astoria-d/super-duper-nes/doc/us-keyboard.png

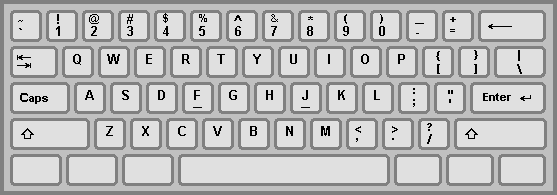
doc/us-keyboard.png
