astoria-d/super-duper-nes/doc/craft-work-diary/20161218/IMG_1332.JPG

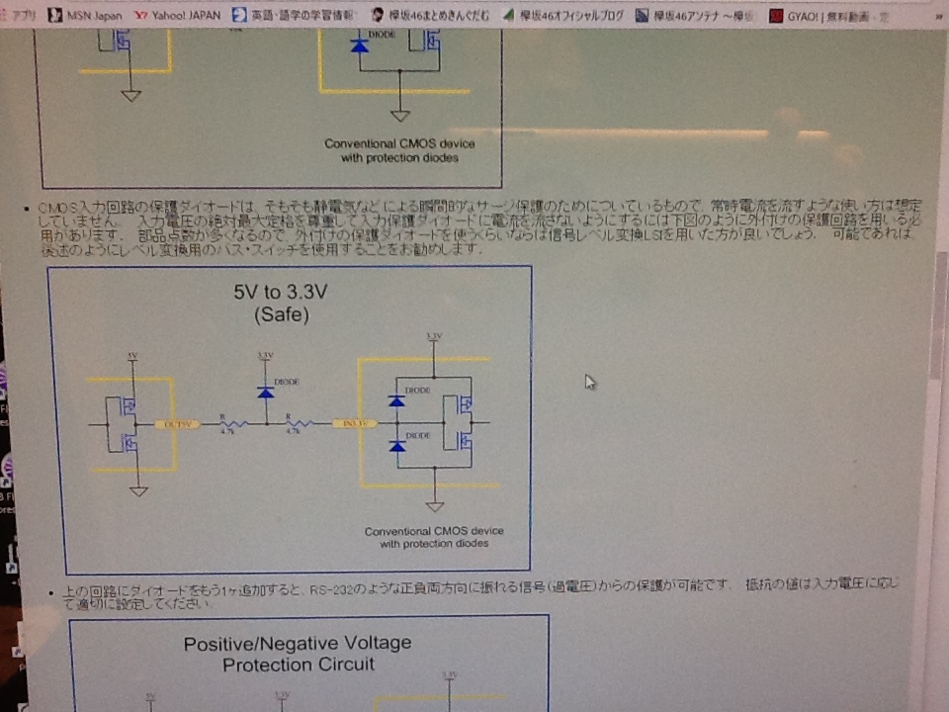
doc/craft-work-diary/20161218/IMG_1332.JPG
