astoria-d/super-duper-nes/doc/craft-work-diary/20161218/IMG_1335.JPG

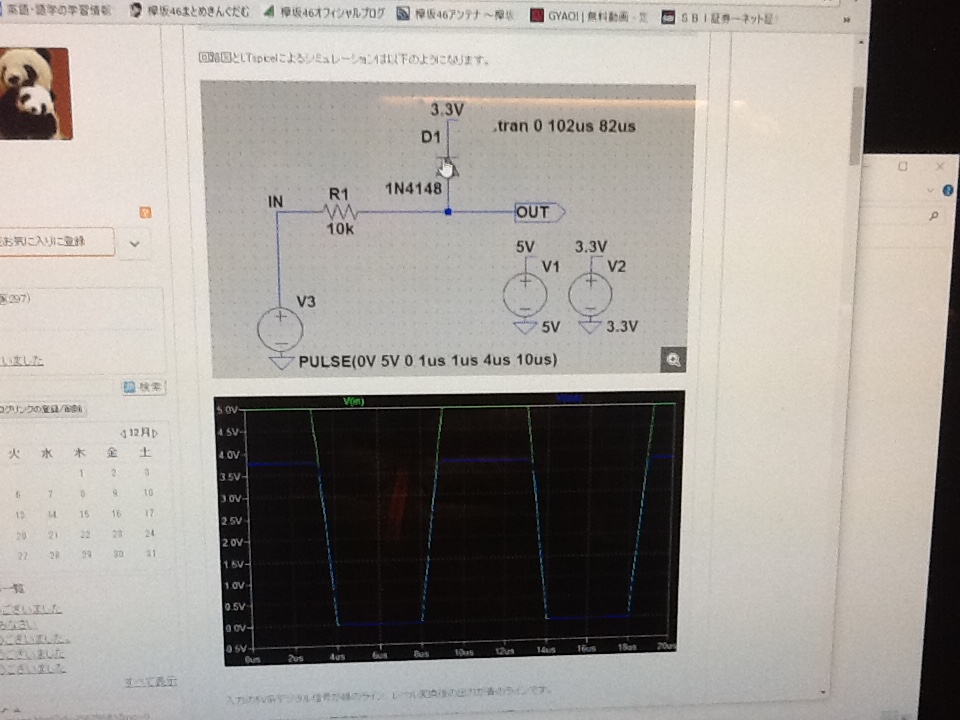
doc/craft-work-diary/20161218/IMG_1335.JPG
