astoria-d/super-duper-nes/doc/craft-work-diary/20161224/IMG_1348.JPG

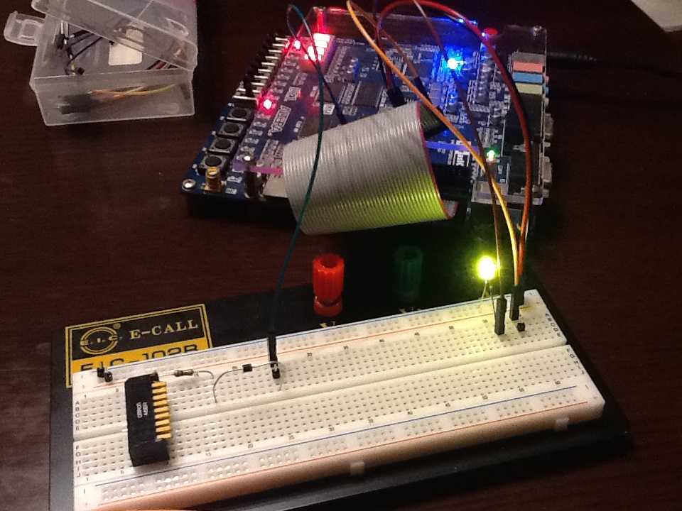
doc/craft-work-diary/20161224/IMG_1348.JPG
