astoria-d/super-duper-nes/doc/craft-work-diary/20161224/IMG_1349.JPG

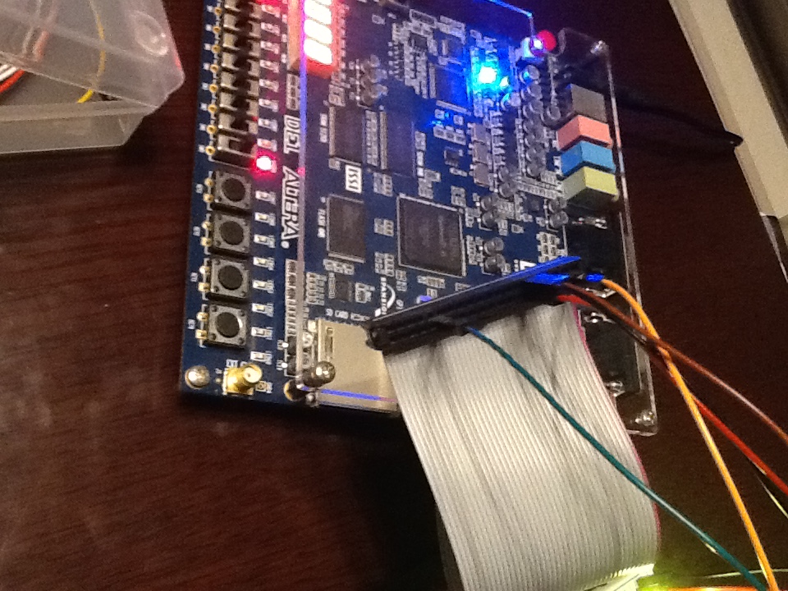
doc/craft-work-diary/20161224/IMG_1349.JPG
