astoria-d/super-duper-nes/doc/craft-work-diary/20161224/IMG_1350.JPG

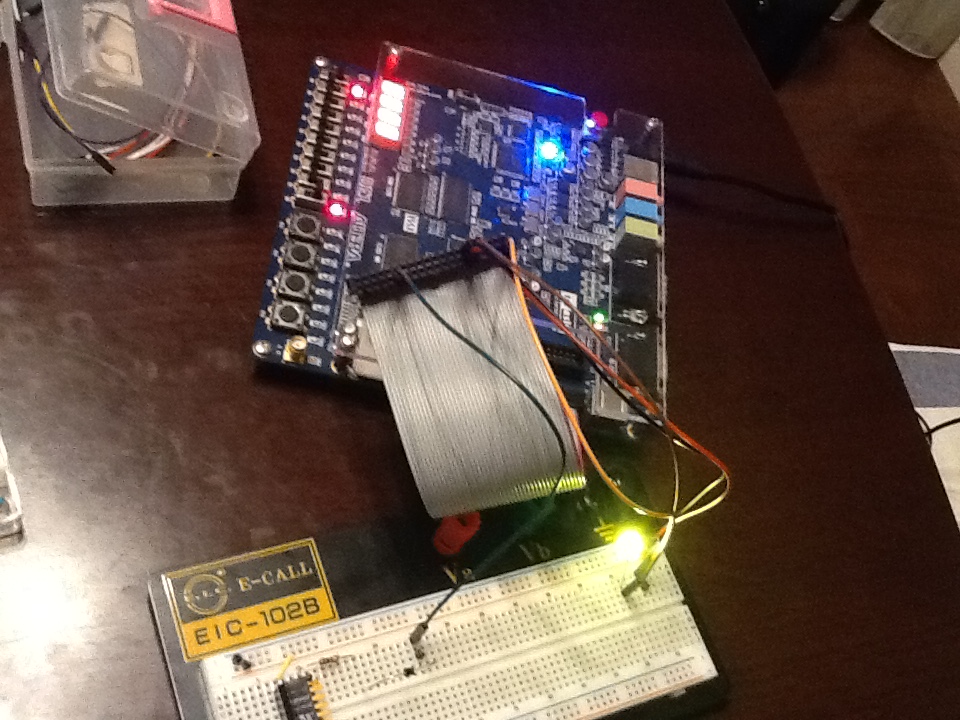
doc/craft-work-diary/20161224/IMG_1350.JPG
