astoria-d/super-duper-nes/doc/craft-work-diary/20161225/IMG_1356.JPG

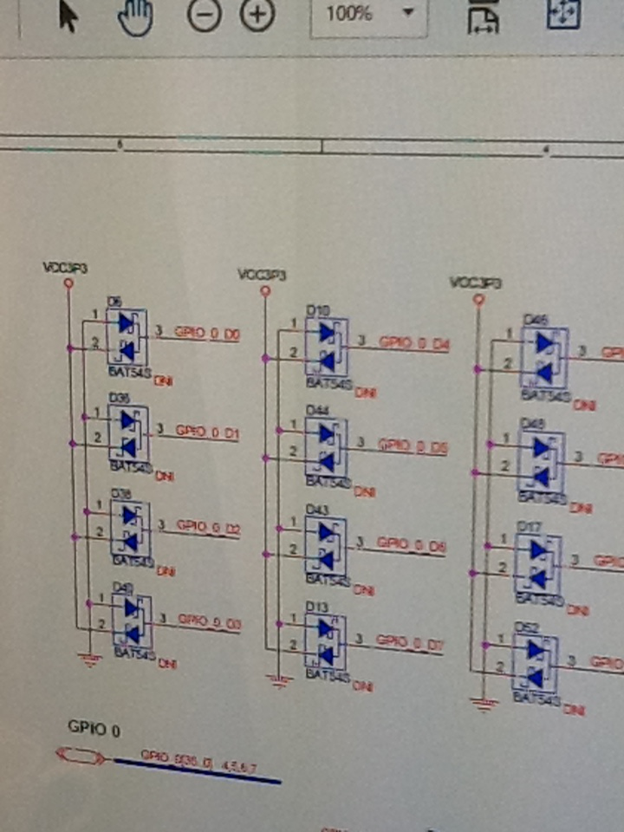
doc/craft-work-diary/20161225/IMG_1356.JPG
