astoria-d/super-duper-nes/doc/craft-work-diary/20161225/IMG_1360.JPG

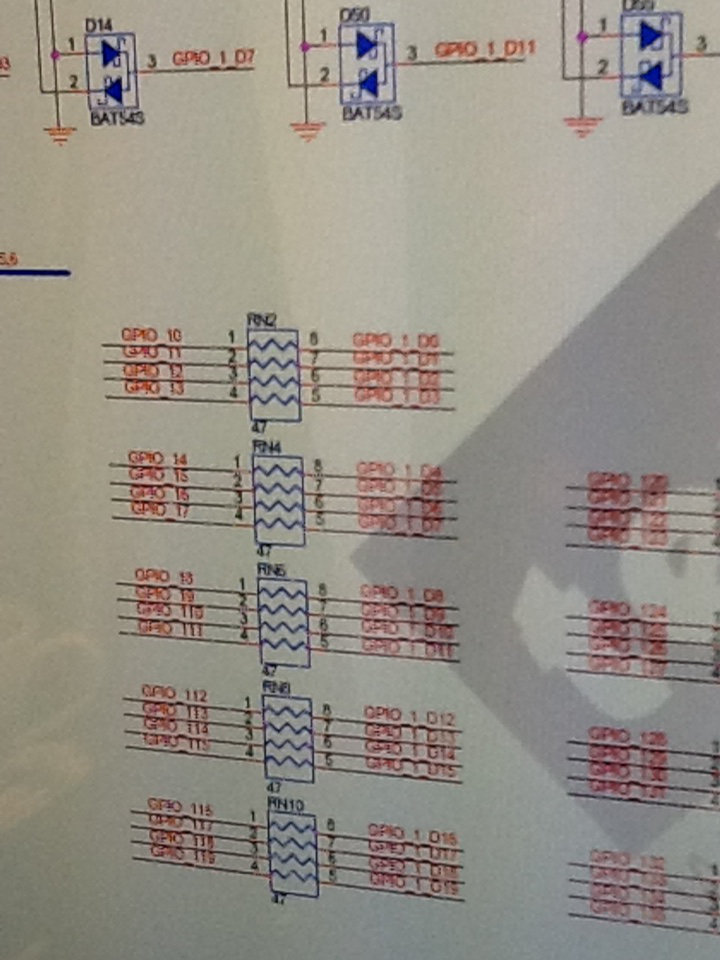
doc/craft-work-diary/20161225/IMG_1360.JPG
