astoria-d/super-duper-nes/doc/craft-work-diary/20161225/IMG_1362.JPG

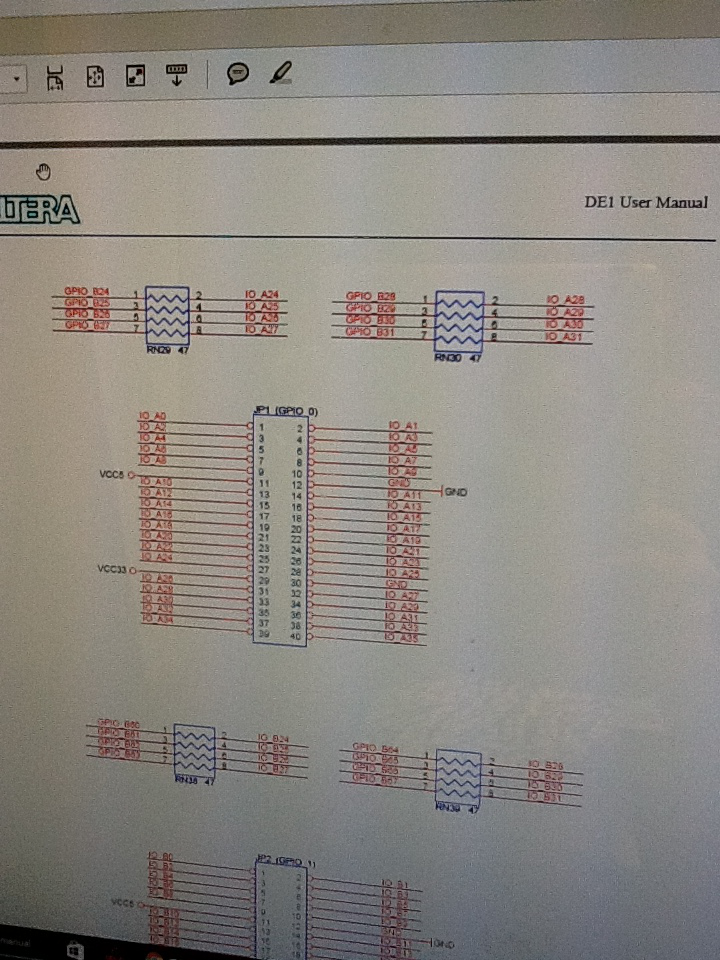
doc/craft-work-diary/20161225/IMG_1362.JPG
