astoria-d/super-duper-nes/doc/craft-work-diary/20170103/IMG_1378.JPG

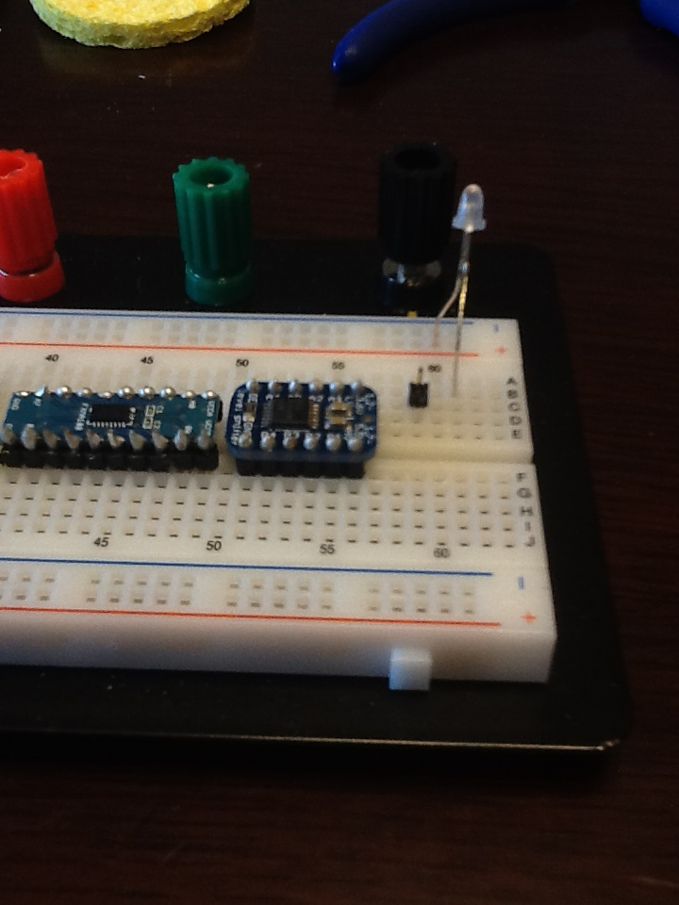
doc/craft-work-diary/20170103/IMG_1378.JPG
