astoria-d/super-duper-nes/doc/craft-work-diary/20170103/IMG_1380.JPG

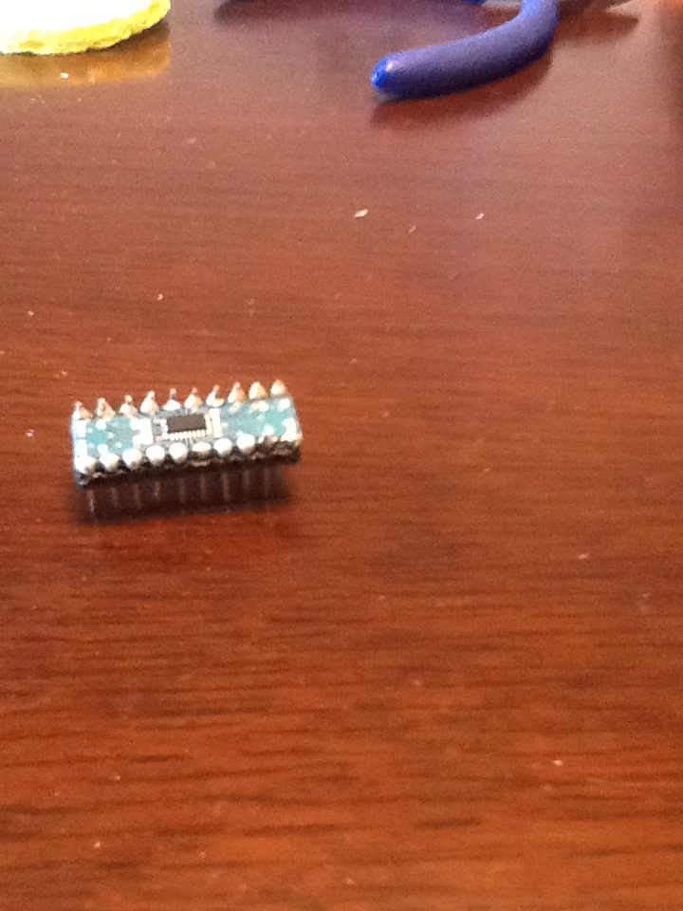
doc/craft-work-diary/20170103/IMG_1380.JPG
