astoria-d/super-duper-nes/doc/craft-work-diary/20170103/IMG_1381.JPG

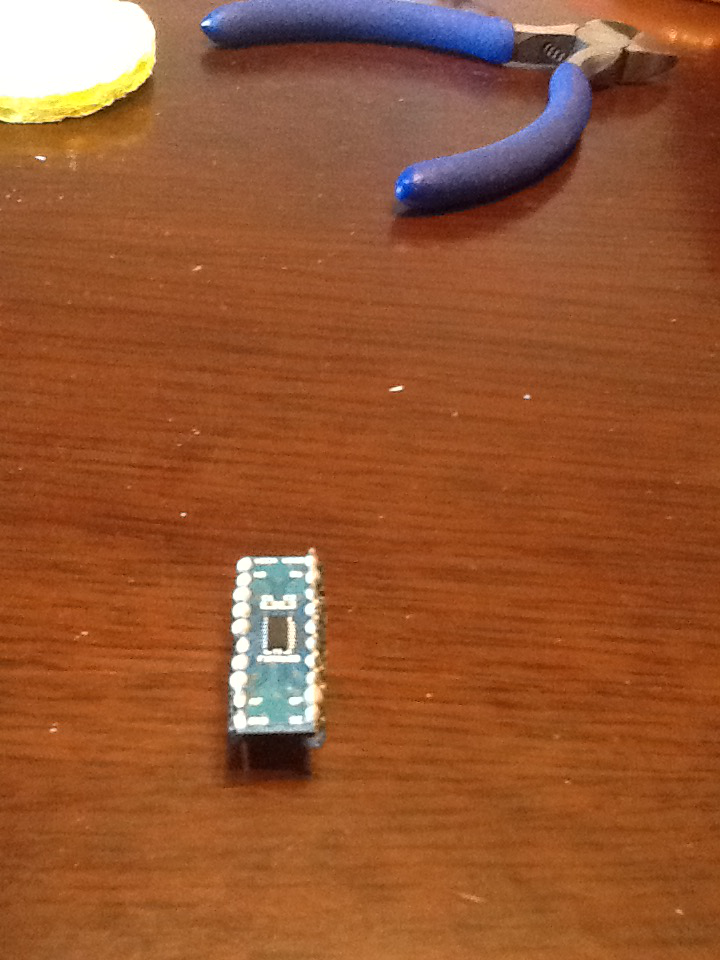
doc/craft-work-diary/20170103/IMG_1381.JPG
