astoria-d/super-duper-nes/doc/craft-work-diary/20170103/IMG_1382.JPG

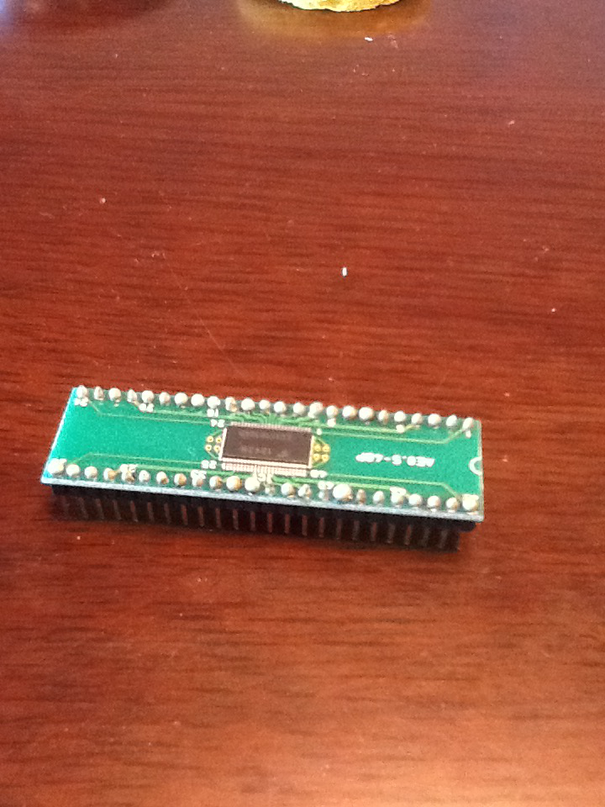
doc/craft-work-diary/20170103/IMG_1382.JPG
