astoria-d/super-duper-nes/doc/craft-work-diary/20170104/IMG_1393.JPG

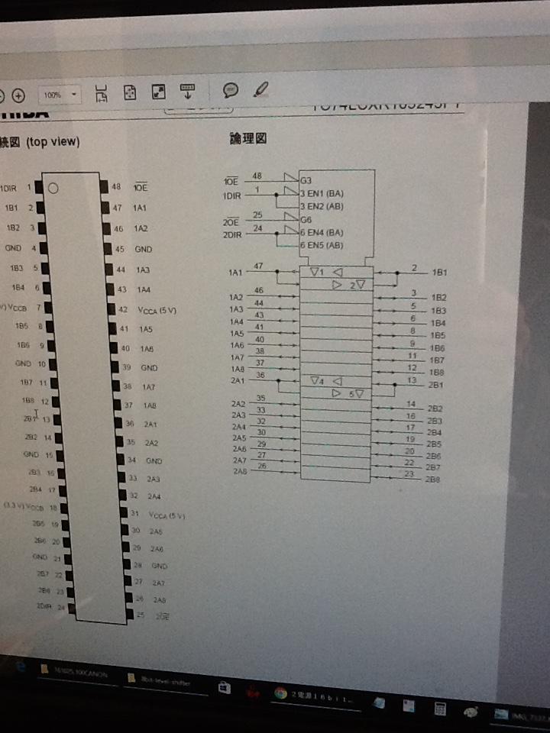
doc/craft-work-diary/20170104/IMG_1393.JPG
