astoria-d/super-duper-nes/doc/craft-work-diary/20170104/IMG_1396.JPG

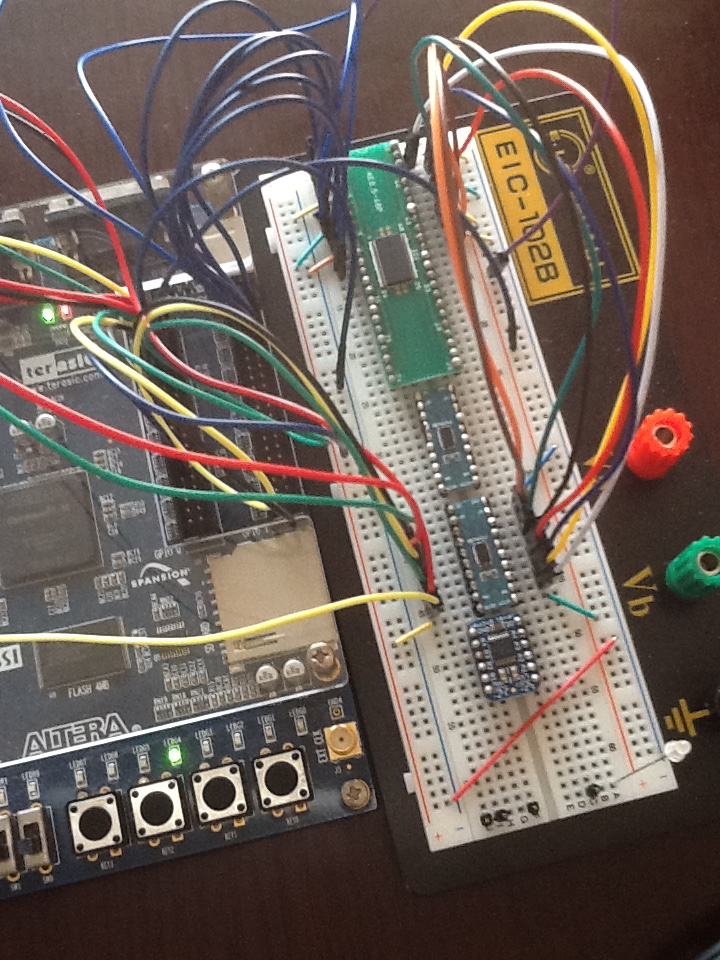
doc/craft-work-diary/20170104/IMG_1396.JPG
