astoria-d/super-duper-nes/doc/craft-work-diary/20170104/IMG_1401.JPG

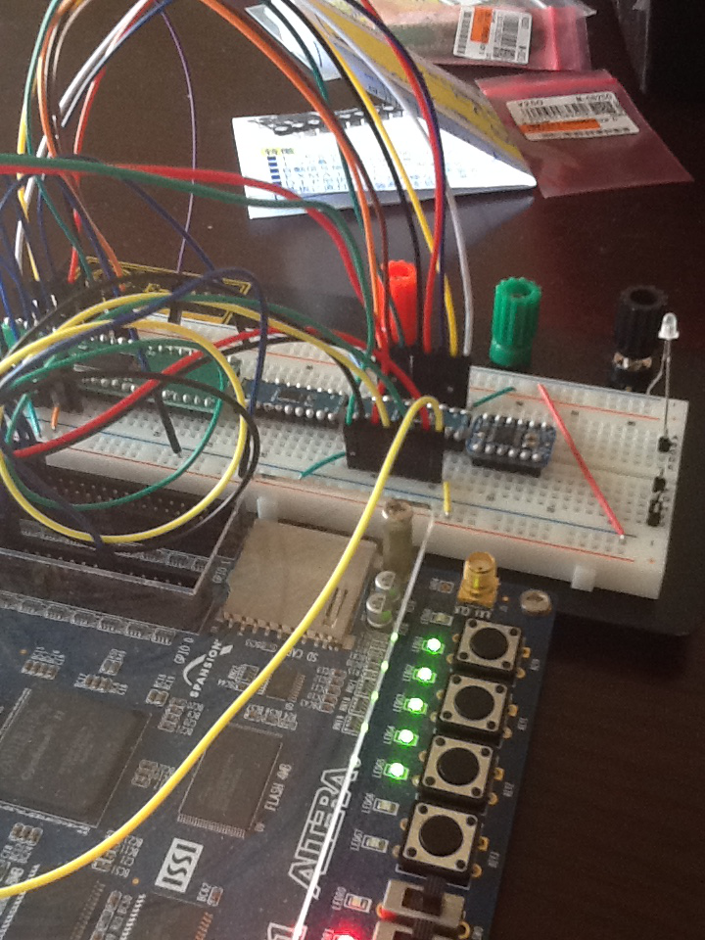
doc/craft-work-diary/20170104/IMG_1401.JPG
