astoria-d/super-duper-nes/doc/craft-work-diary/20170104/IMG_1402.JPG

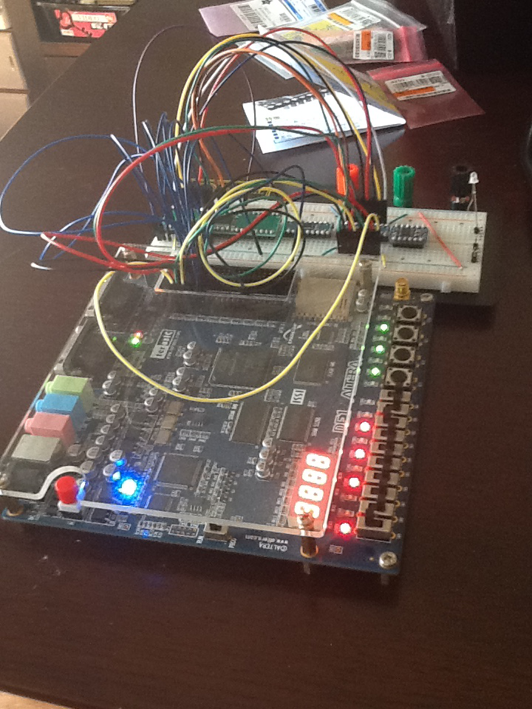
doc/craft-work-diary/20170104/IMG_1402.JPG
