astoria-d/super-duper-nes/doc/craft-work-diary/20170107/IMG_1409.JPG

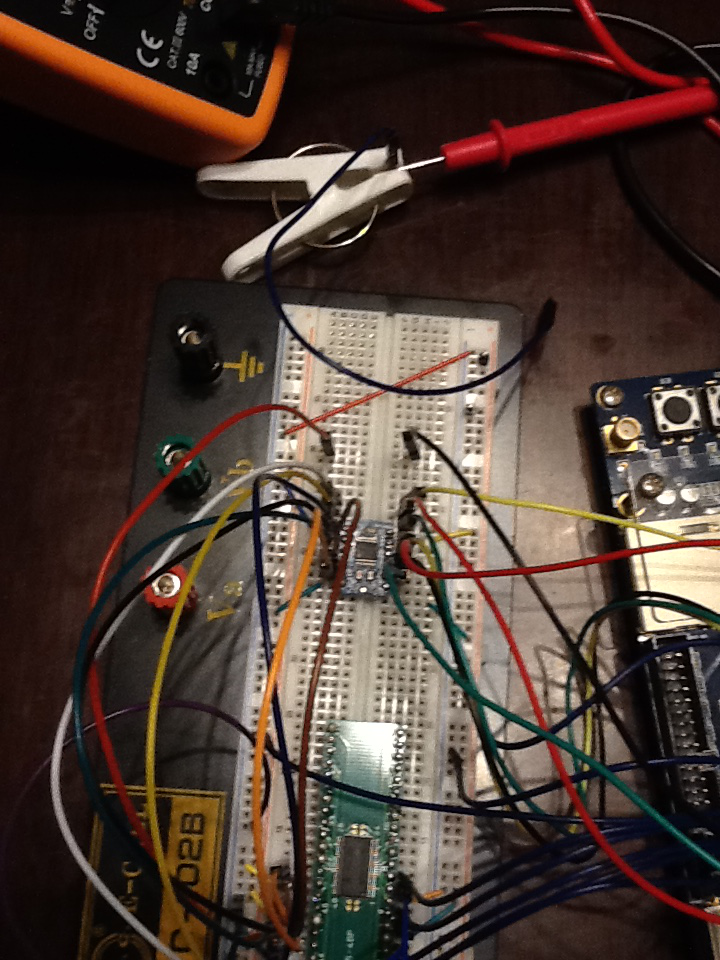
doc/craft-work-diary/20170107/IMG_1409.JPG
