astoria-d/super-duper-nes/doc/craft-work-diary/20170108/IMG_1414.JPG

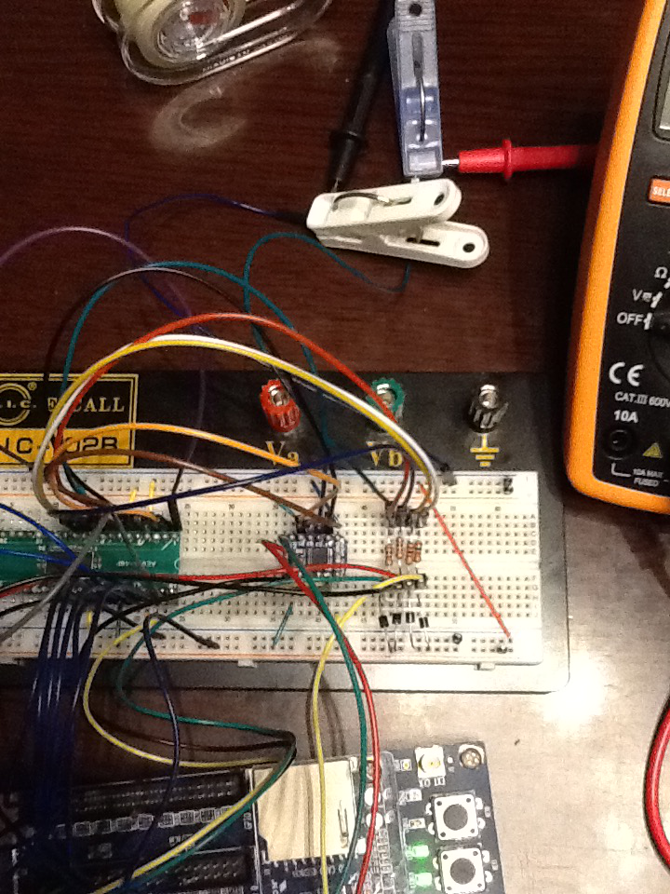
doc/craft-work-diary/20170108/IMG_1414.JPG
