astoria-d/super-duper-nes/doc/craft-work-diary/20170109/IMG_1426.PNG

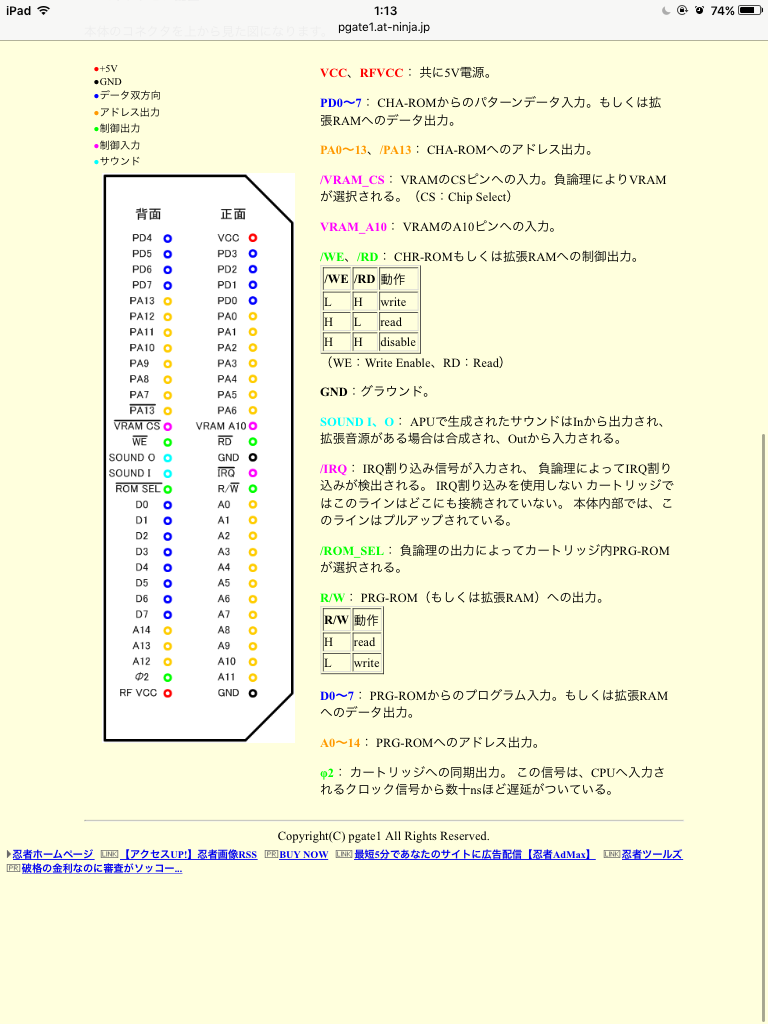
doc/craft-work-diary/20170109/IMG_1426.PNG
