astoria-d/super-duper-nes/doc/craft-work-diary/20170109/IMG_1438.JPG

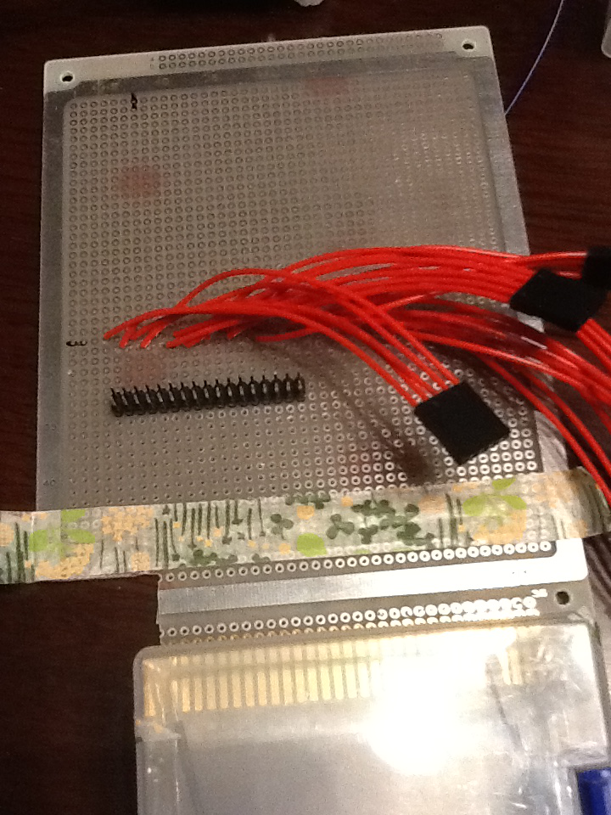
doc/craft-work-diary/20170109/IMG_1438.JPG
