astoria-d/super-duper-nes/doc/craft-work-diary/20170109/IMG_1439.JPG

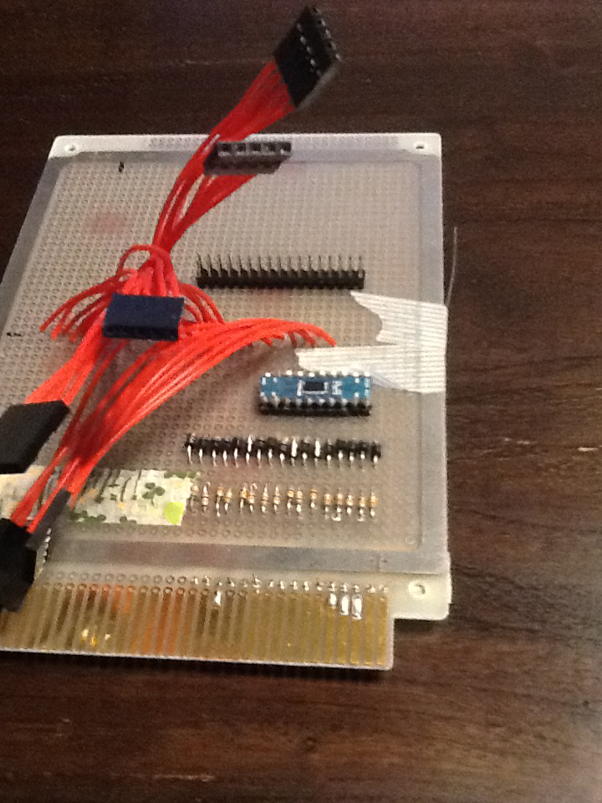
doc/craft-work-diary/20170109/IMG_1439.JPG
