astoria-d/super-duper-nes/doc/craft-work-diary/20170110/IMG_1443.JPG

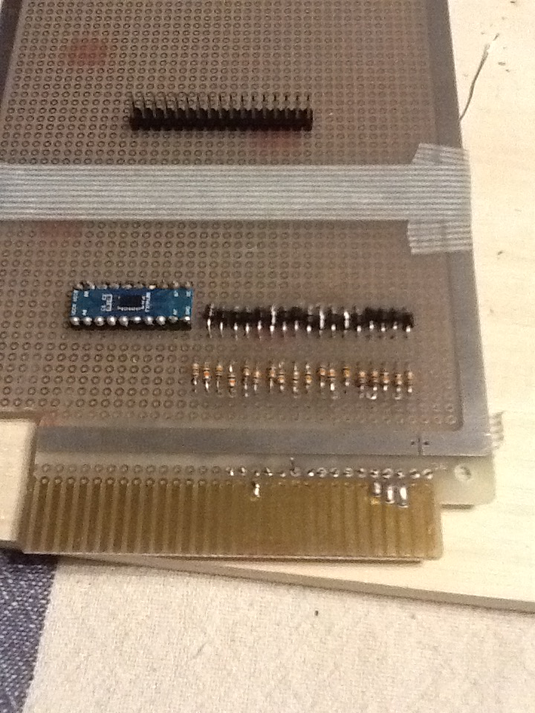
doc/craft-work-diary/20170110/IMG_1443.JPG
