astoria-d/super-duper-nes/doc/craft-work-diary/20170110/IMG_1444.JPG

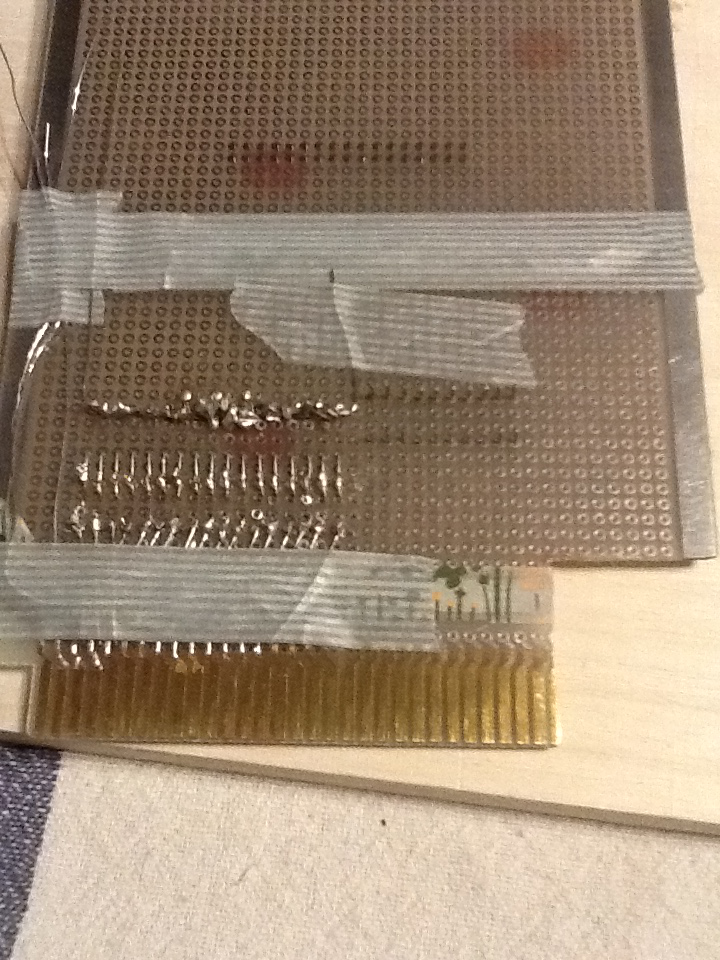
doc/craft-work-diary/20170110/IMG_1444.JPG
