astoria-d/super-duper-nes/doc/craft-work-diary/20170114/IMG_1446.JPG

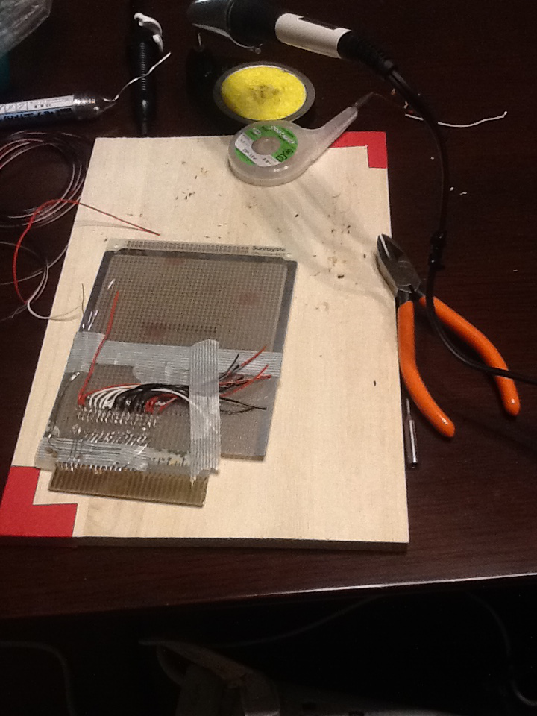
doc/craft-work-diary/20170114/IMG_1446.JPG
