astoria-d/super-duper-nes/doc/craft-work-diary/20170115/IMG_1449.JPG

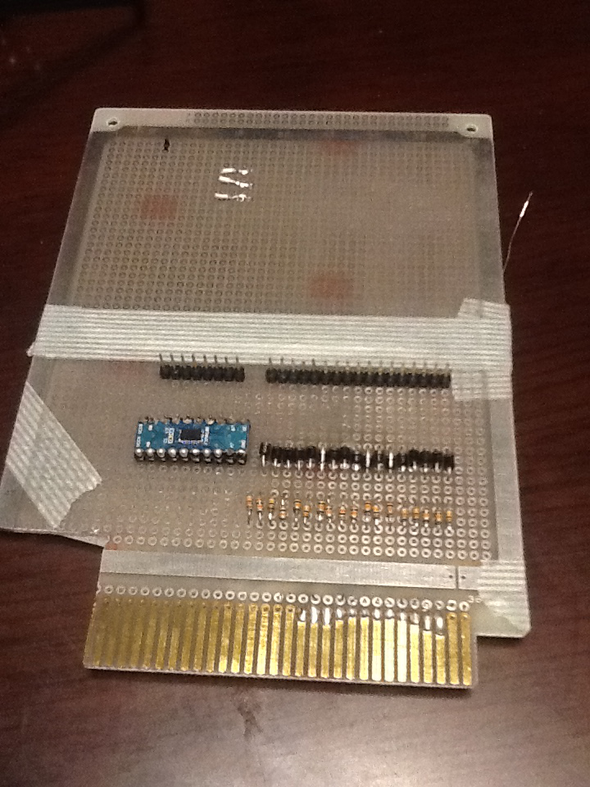
doc/craft-work-diary/20170115/IMG_1449.JPG
