astoria-d/super-duper-nes/doc/craft-work-diary/20170116/IMG_1457.JPG

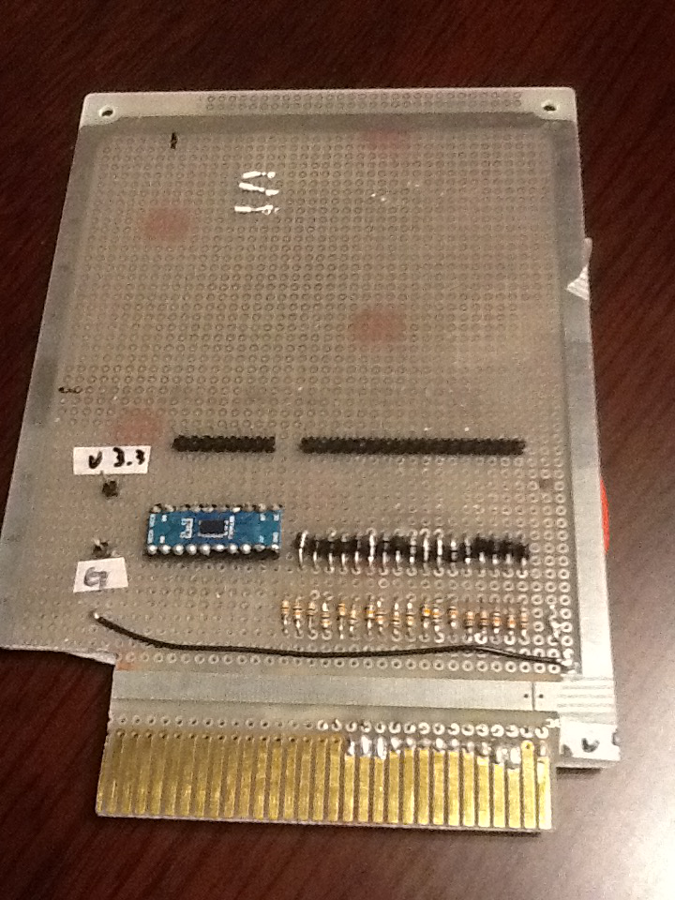
doc/craft-work-diary/20170116/IMG_1457.JPG
