astoria-d/super-duper-nes/doc/craft-work-diary/20170119/IMG_1460.JPG

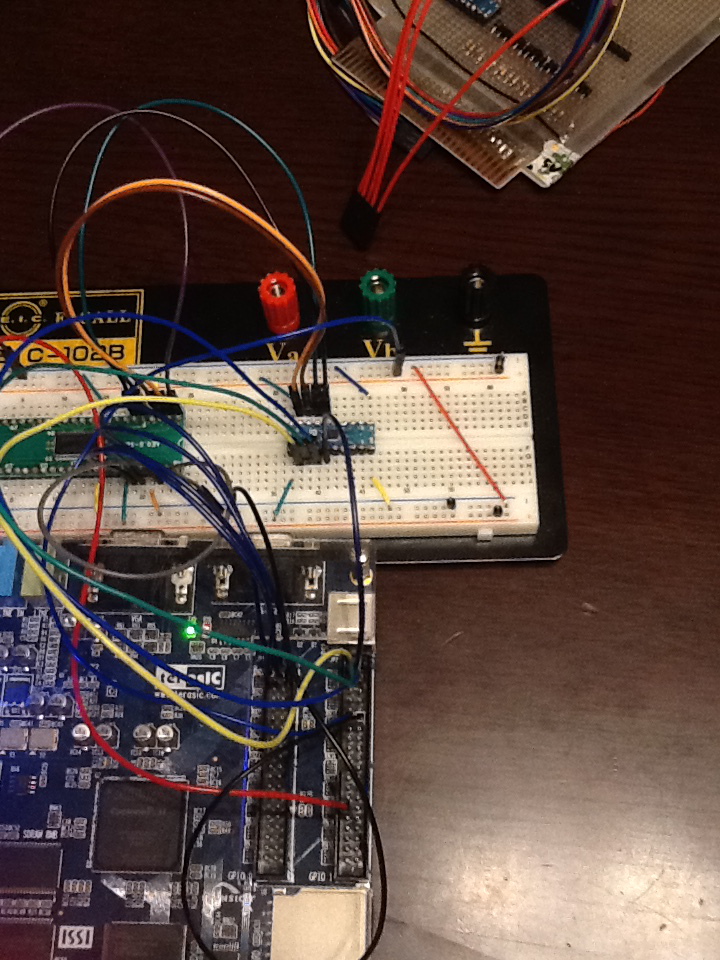
doc/craft-work-diary/20170119/IMG_1460.JPG
