astoria-d/super-duper-nes/doc/craft-work-diary/20170121/IMG_1466.JPG

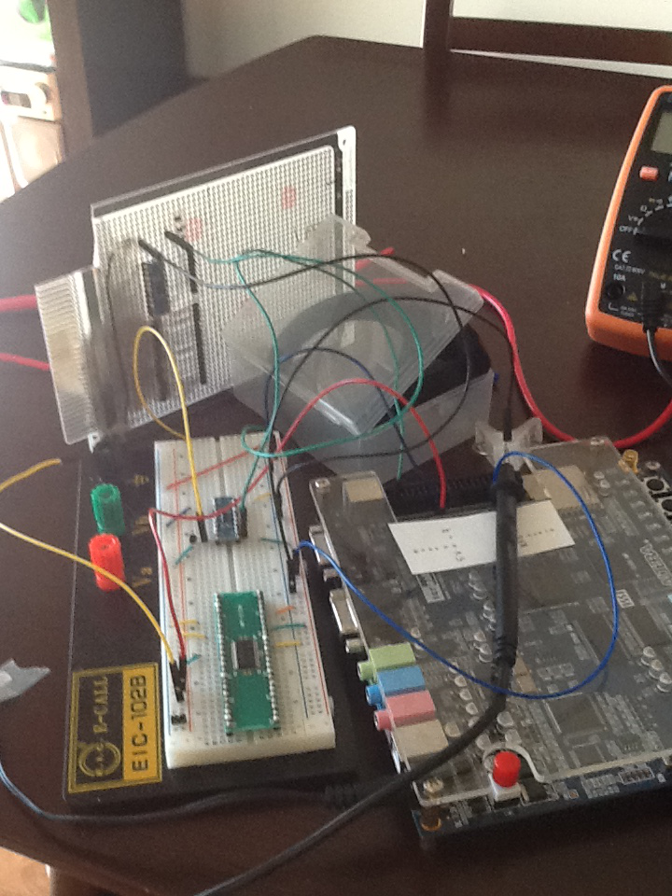
doc/craft-work-diary/20170121/IMG_1466.JPG
