astoria-d/super-duper-nes/doc/craft-work-diary/20170121/IMG_1471.JPG

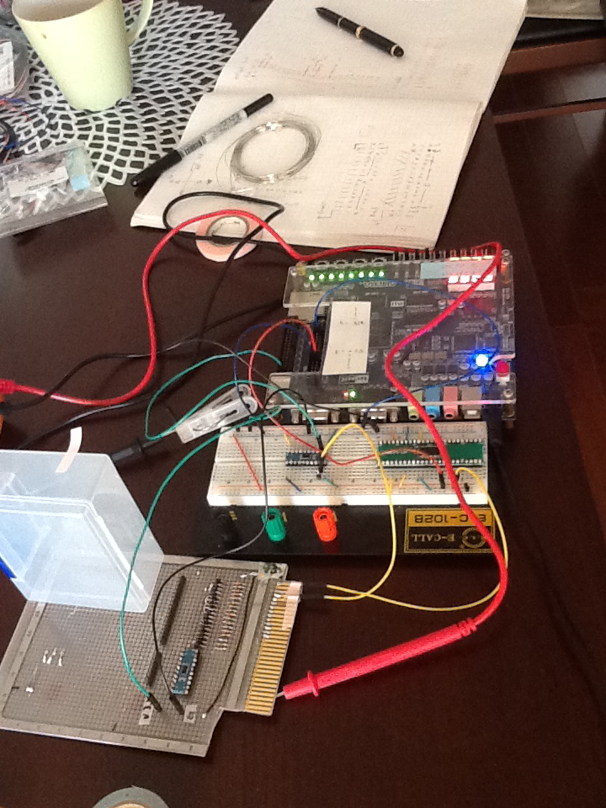
doc/craft-work-diary/20170121/IMG_1471.JPG
