astoria-d/super-duper-nes/doc/craft-work-diary/20170122/IMG_1478.JPG

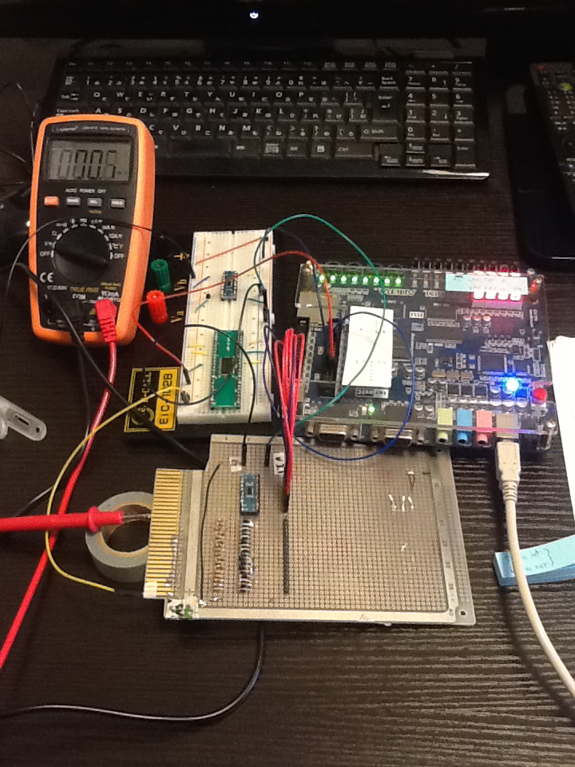
doc/craft-work-diary/20170122/IMG_1478.JPG
