astoria-d/super-duper-nes/doc/craft-work-diary/20170122/IMG_1479.JPG

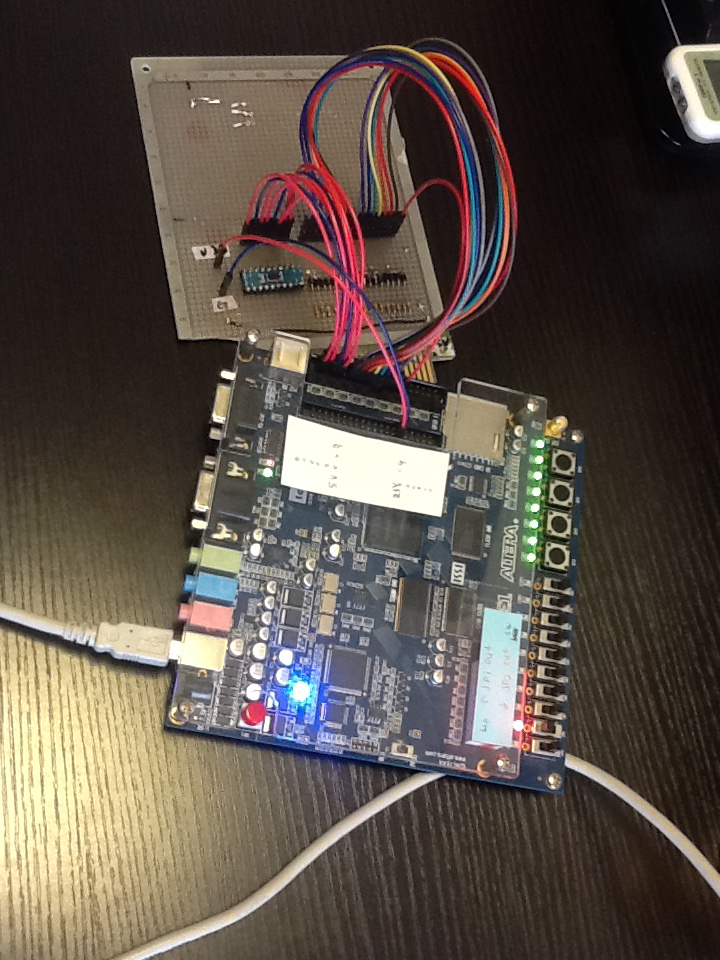
doc/craft-work-diary/20170122/IMG_1479.JPG
