astoria-d/super-duper-nes/doc/craft-work-diary/20170129/IMG_1487.JPG

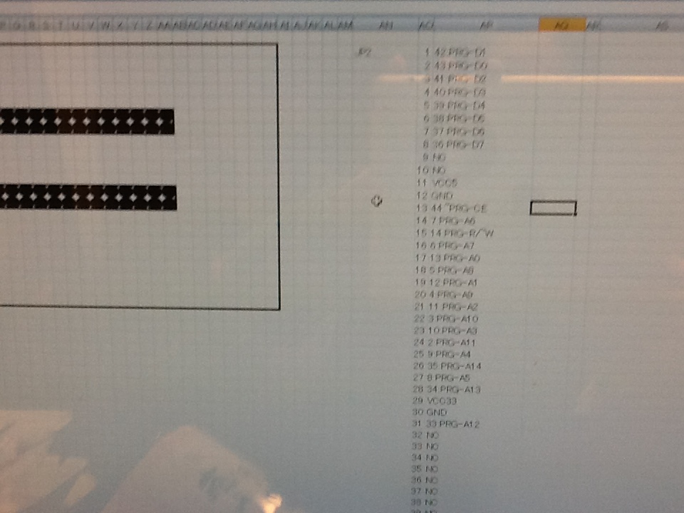
doc/craft-work-diary/20170129/IMG_1487.JPG
