astoria-d/super-duper-nes/doc/craft-work-diary/20170129/IMG_1489.JPG

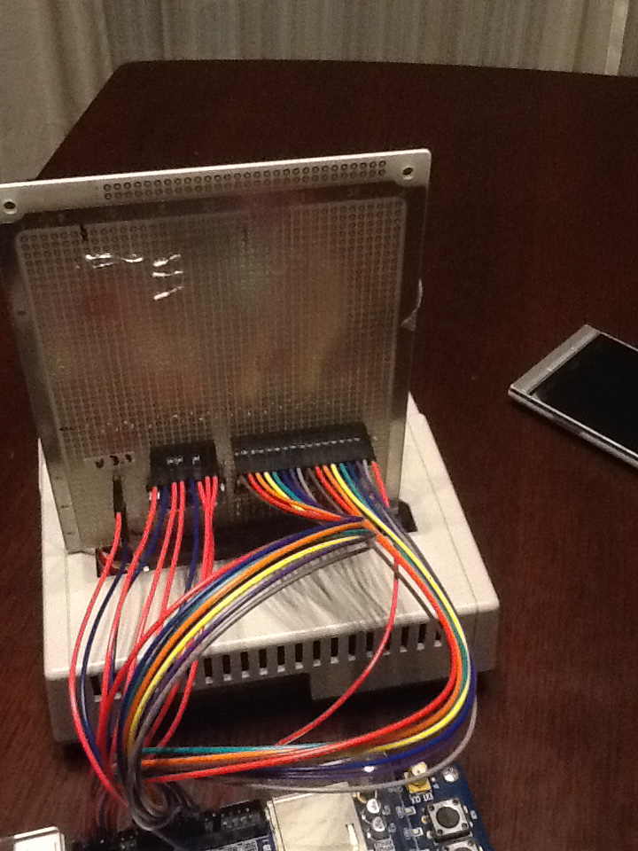
doc/craft-work-diary/20170129/IMG_1489.JPG
