astoria-d/super-duper-nes/doc/craft-work-diary/20170212/IMG_1499.JPG

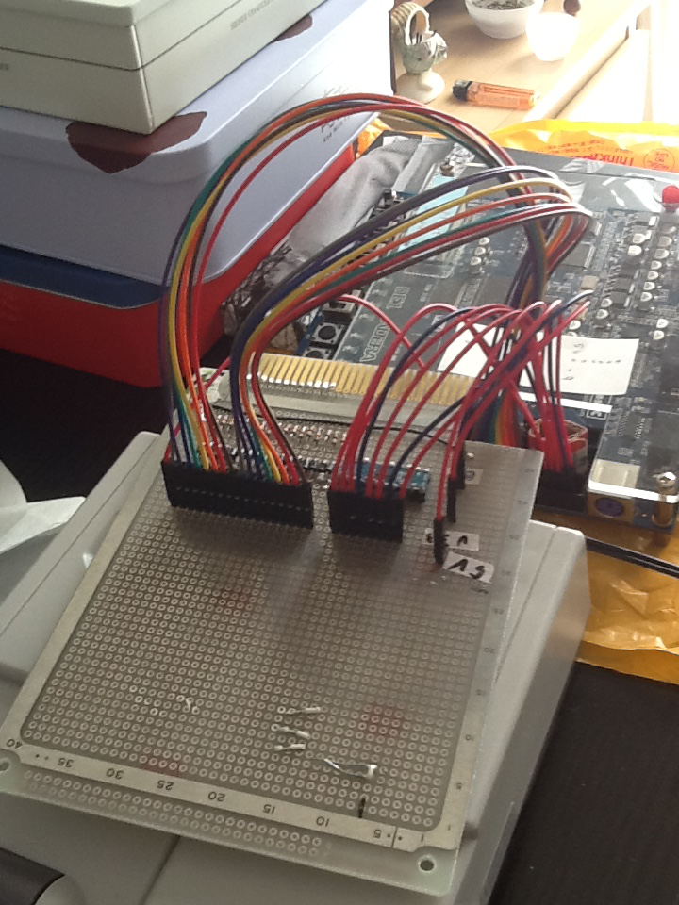
doc/craft-work-diary/20170212/IMG_1499.JPG
