astoria-d/super-duper-nes/doc/craft-work-diary/20170212/IMG_1508.JPG

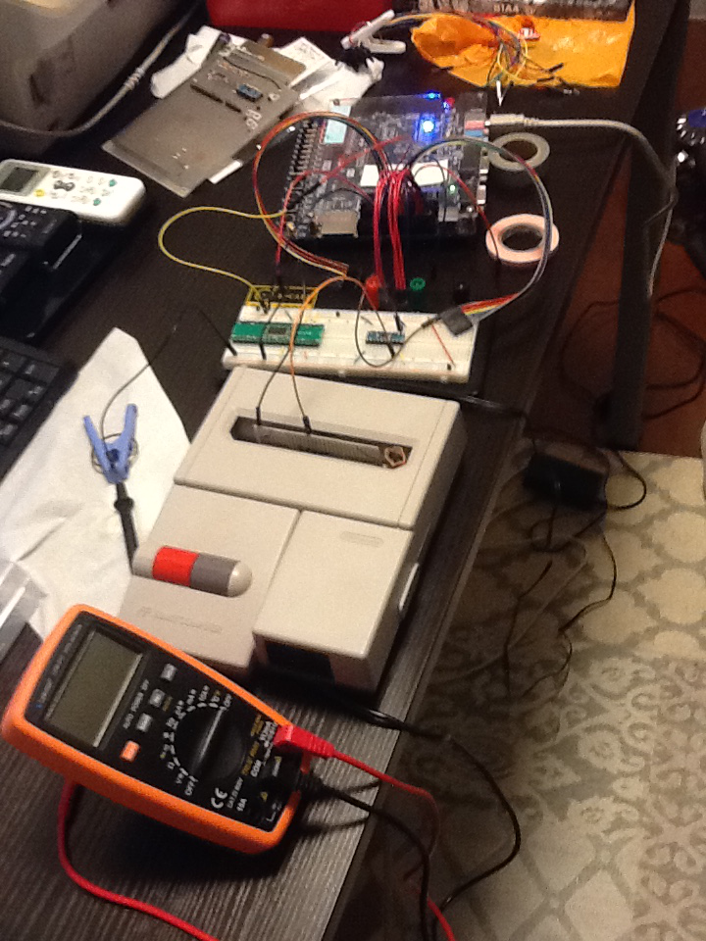
doc/craft-work-diary/20170212/IMG_1508.JPG
