astoria-d/super-duper-nes/doc/craft-work-diary/20170218/IMG_1511.JPG

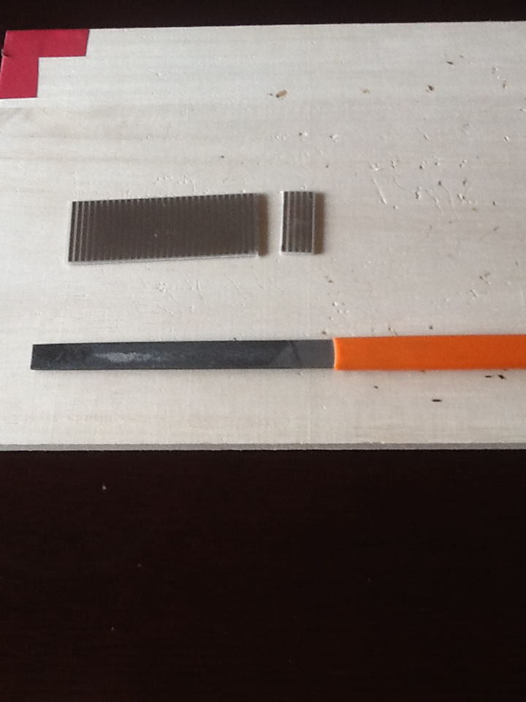
doc/craft-work-diary/20170218/IMG_1511.JPG
