astoria-d/super-duper-nes/doc/craft-work-diary/20170219/IMG_1532.JPG

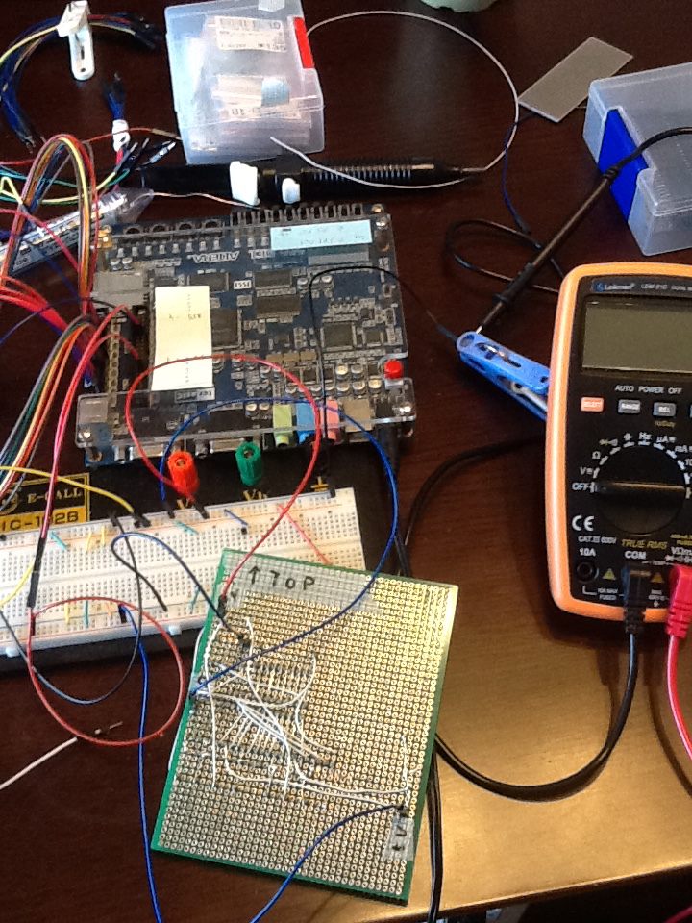
doc/craft-work-diary/20170219/IMG_1532.JPG
