astoria-d/super-duper-nes/doc/craft-work-diary/20170226/IMG_1553.JPG

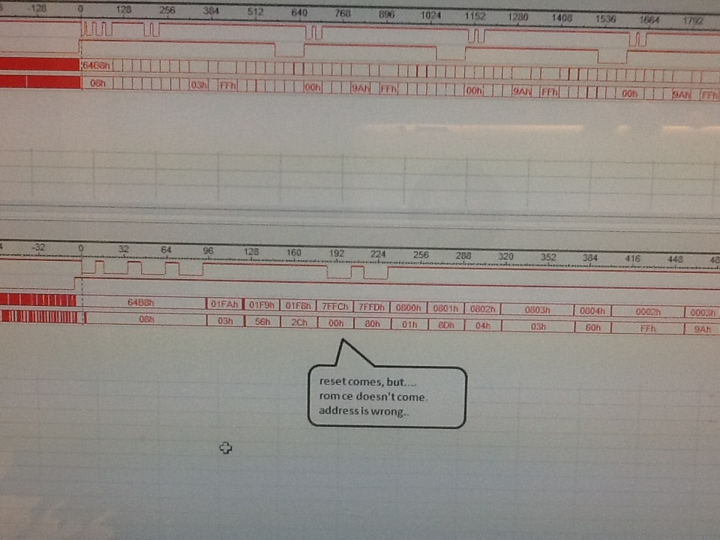
doc/craft-work-diary/20170226/IMG_1553.JPG
