astoria-d/super-duper-nes/doc/craft-work-diary/20170304/IMG_1560.JPG

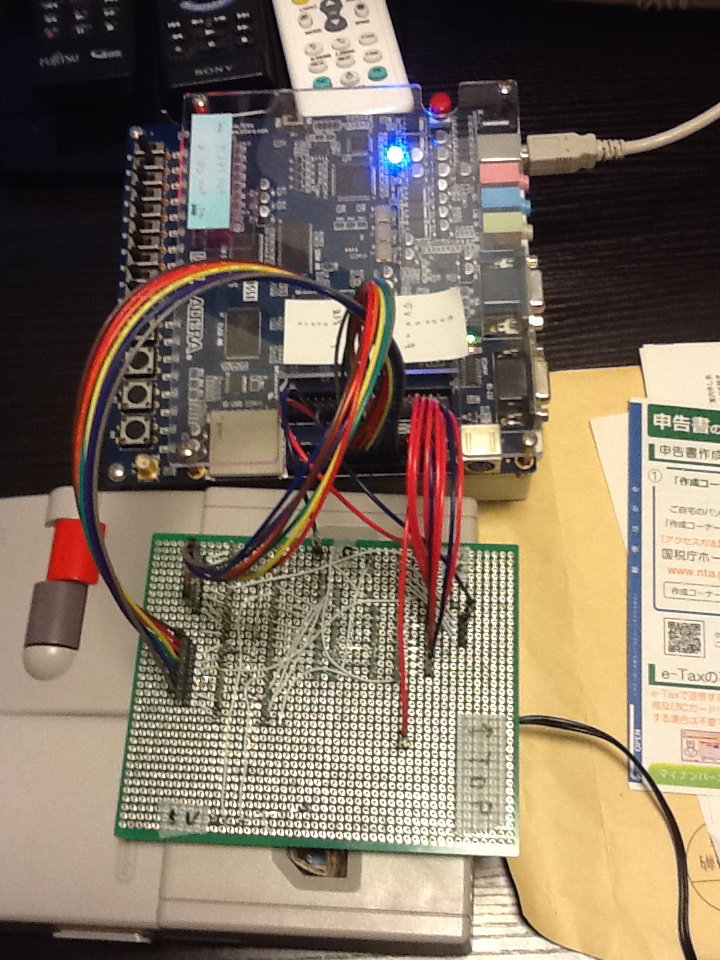
doc/craft-work-diary/20170304/IMG_1560.JPG
