astoria-d/super-duper-nes/doc/craft-work-diary/20170305/IMG_1566.JPG

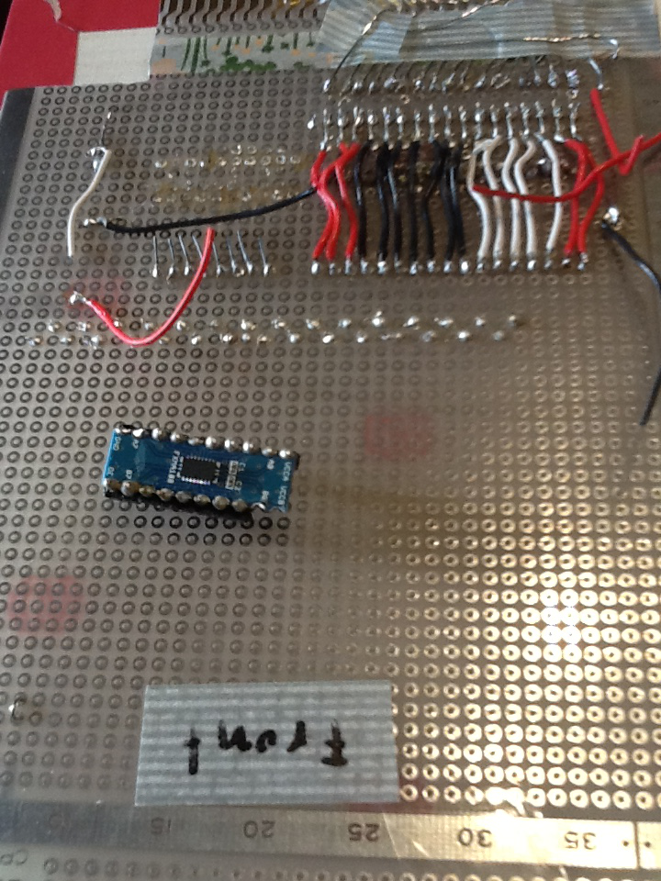
doc/craft-work-diary/20170305/IMG_1566.JPG
