astoria-d/super-duper-nes/doc/craft-work-diary/20170305/IMG_1567.JPG

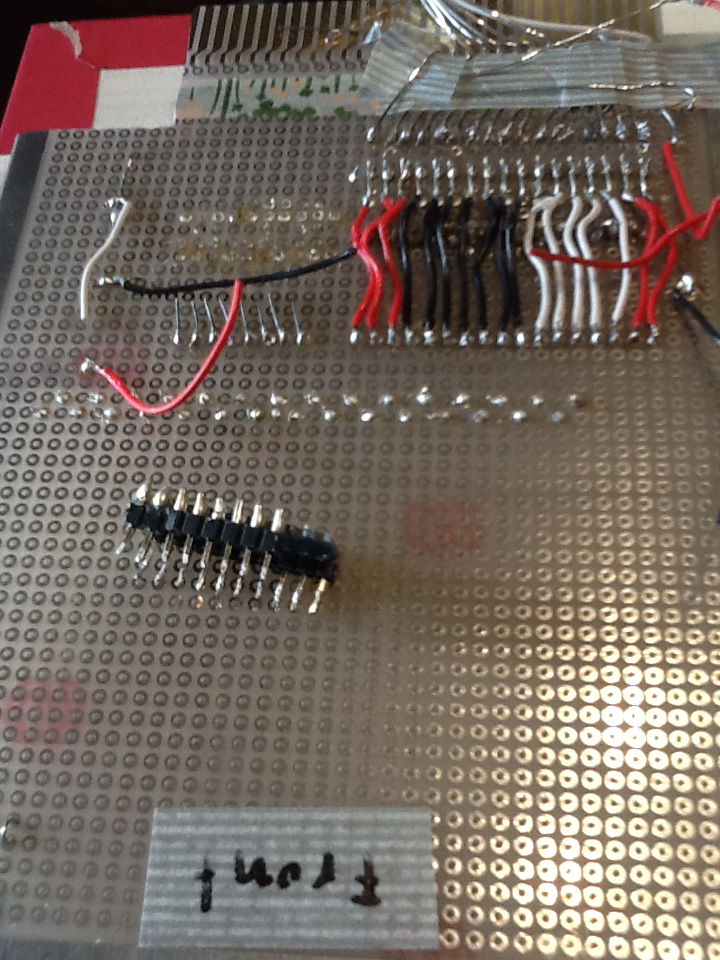
doc/craft-work-diary/20170305/IMG_1567.JPG
