astoria-d/super-duper-nes/doc/craft-work-diary/20170311/IMG_1575.JPG

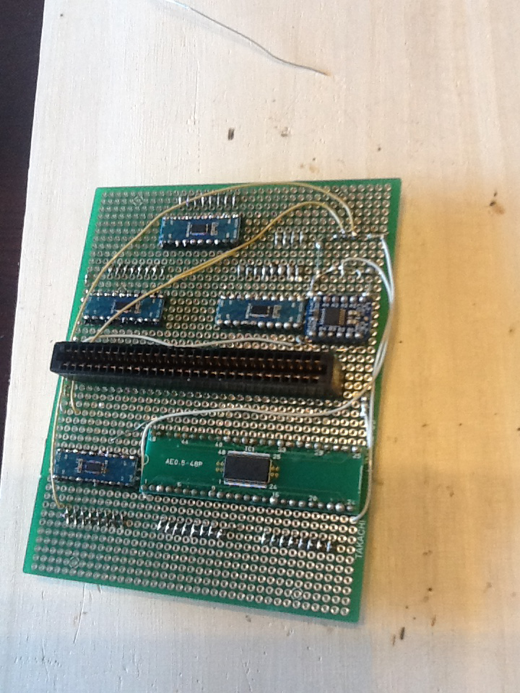
doc/craft-work-diary/20170311/IMG_1575.JPG
