astoria-d/super-duper-nes/doc/craft-work-diary/20170313/IMG_1589.JPG

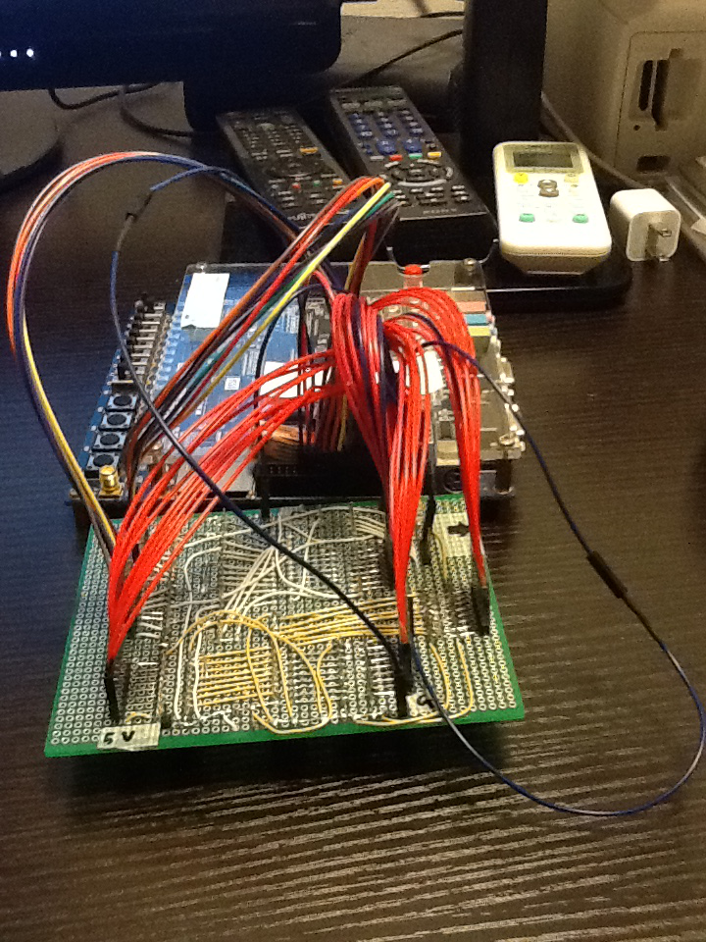
doc/craft-work-diary/20170313/IMG_1589.JPG
