astoria-d/super-duper-nes/doc/craft-work-diary/20170314/IMG_1591.JPG

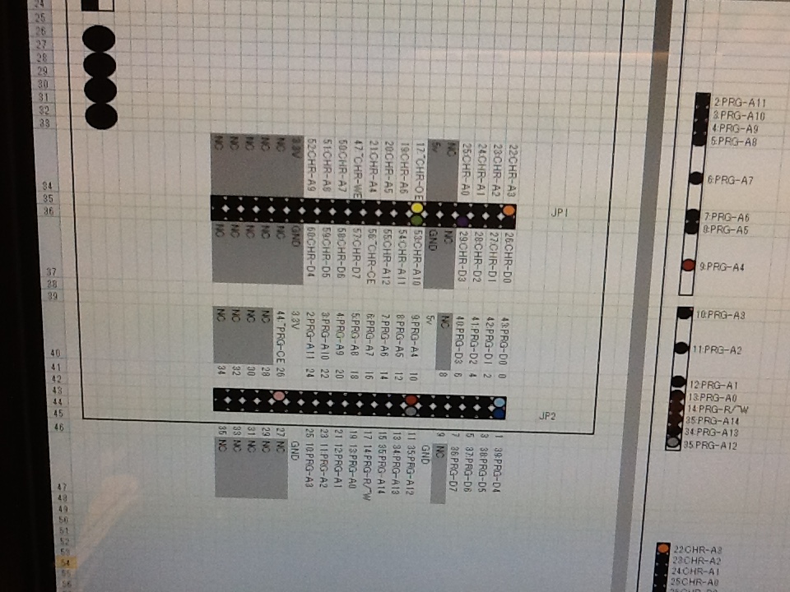
doc/craft-work-diary/20170314/IMG_1591.JPG
