astoria-d/super-duper-nes/doc/craft-work-diary/20170319/IMG_1593.JPG

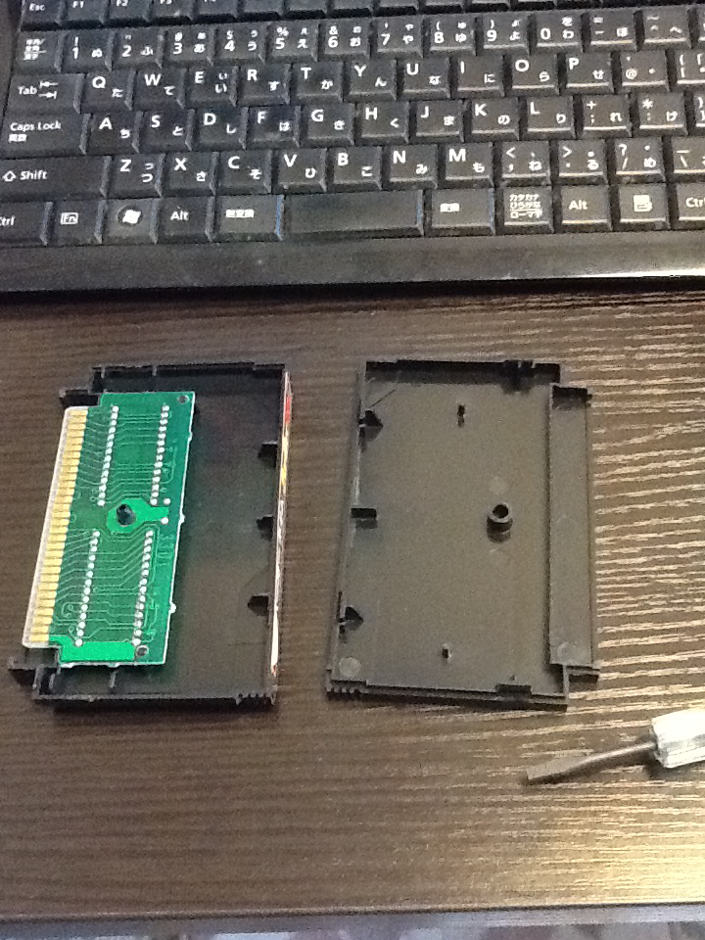
doc/craft-work-diary/20170319/IMG_1593.JPG
