astoria-d/super-duper-nes/doc/craft-work-diary/20170319/IMG_1596.JPG

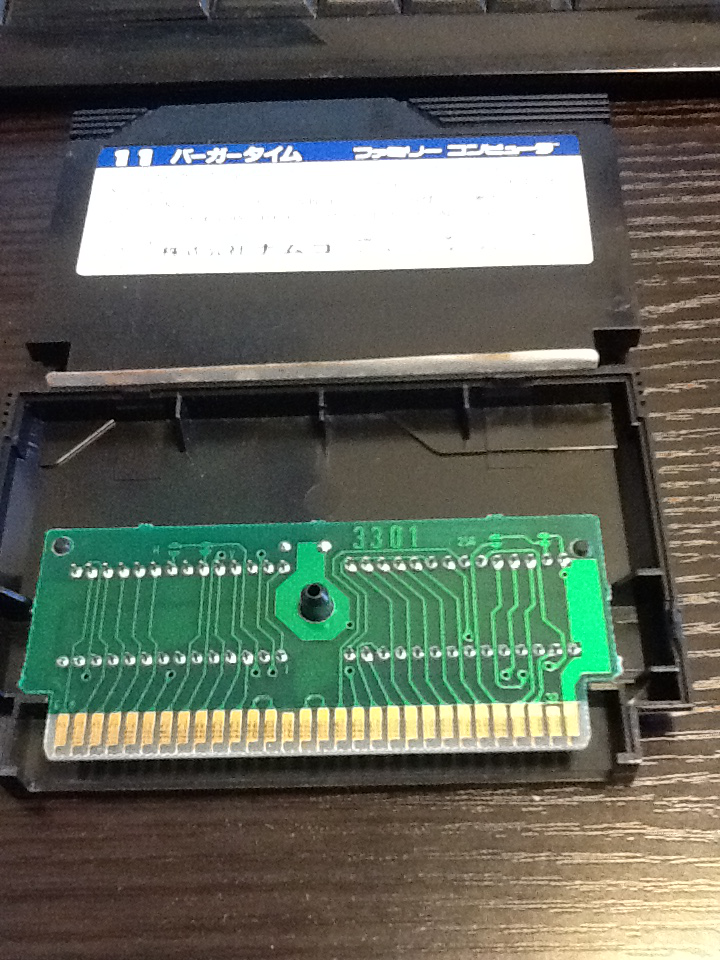
doc/craft-work-diary/20170319/IMG_1596.JPG
