astoria-d/super-duper-nes/doc/craft-work-diary/20170402/IMG_0011.JPG

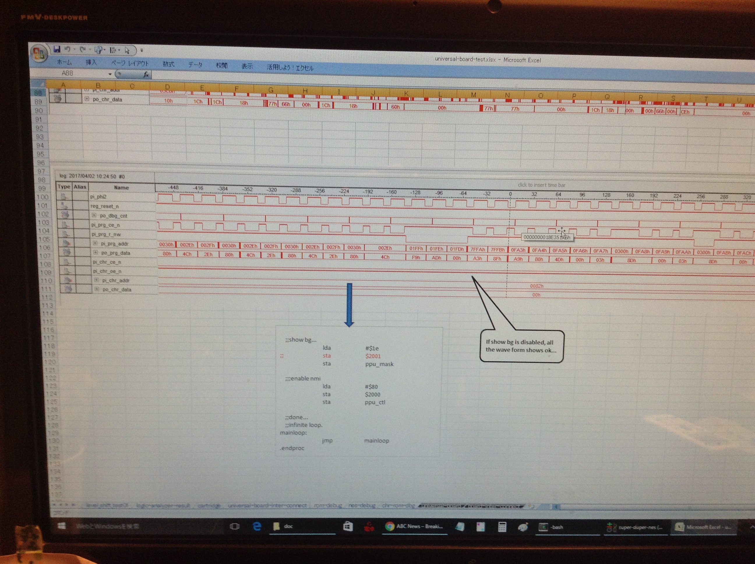
doc/craft-work-diary/20170402/IMG_0011.JPG
