astoria-d/super-duper-nes/doc/craft-work-diary/20170409/IMG_0013.JPG

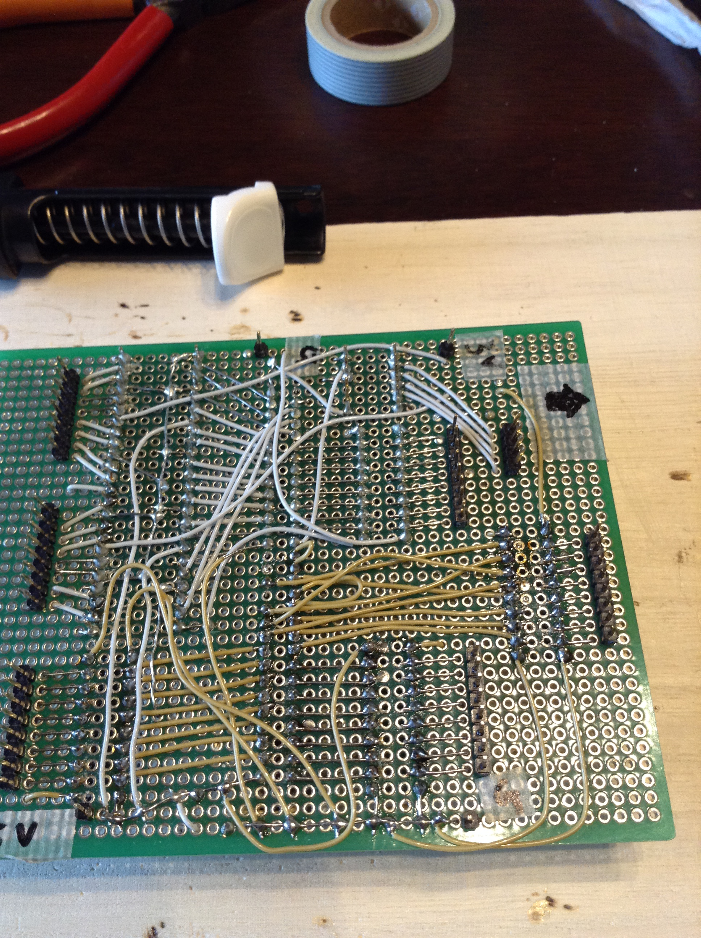
doc/craft-work-diary/20170409/IMG_0013.JPG
