astoria-d/super-duper-nes/doc/craft-work-diary/20170409/IMG_0017.JPG

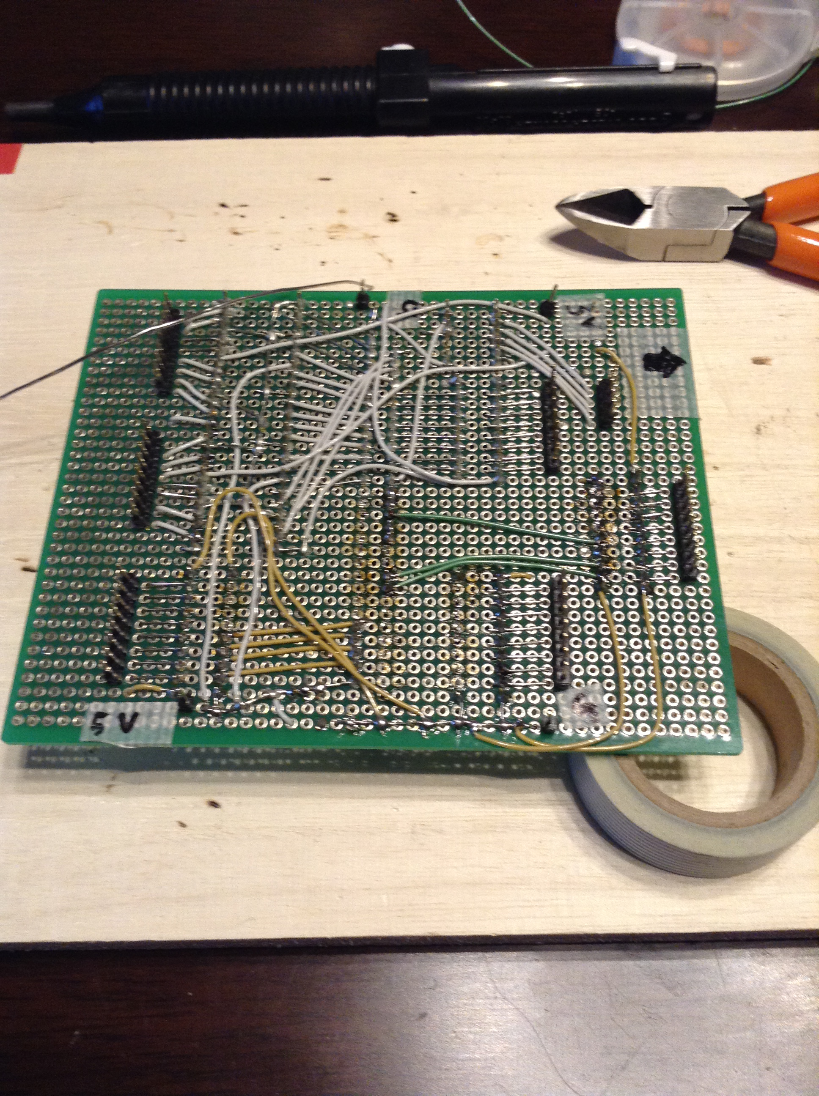
doc/craft-work-diary/20170409/IMG_0017.JPG
