astoria-d/super-duper-nes/doc/craft-work-diary/20170415/IMG_0020.JPG

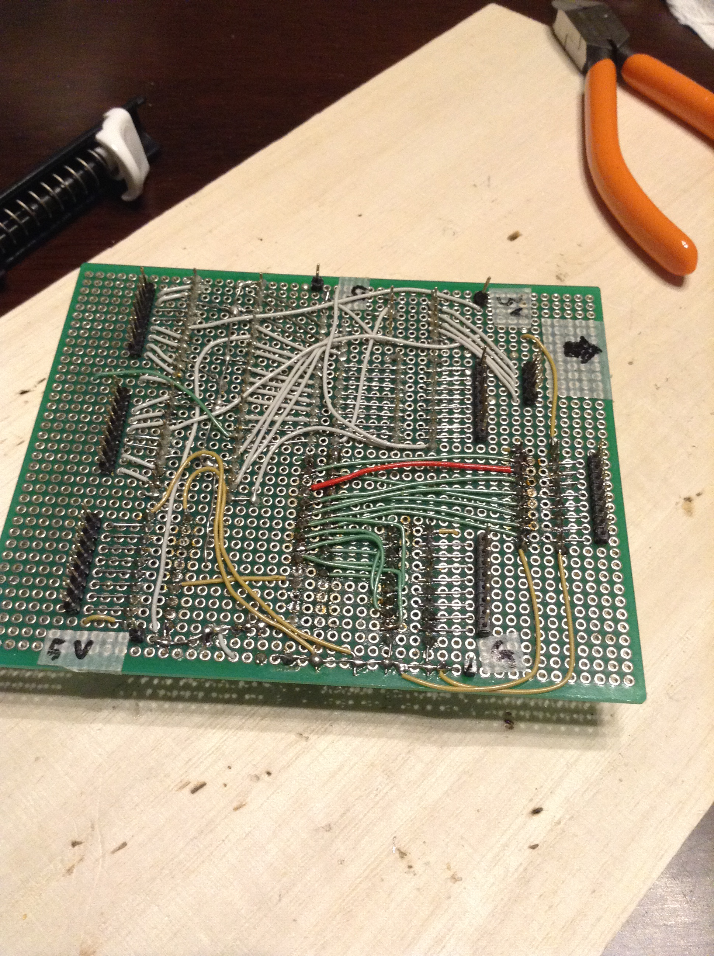
doc/craft-work-diary/20170415/IMG_0020.JPG
