astoria-d/super-duper-nes/doc/craft-work-diary/20170416/IMG_0029.JPG

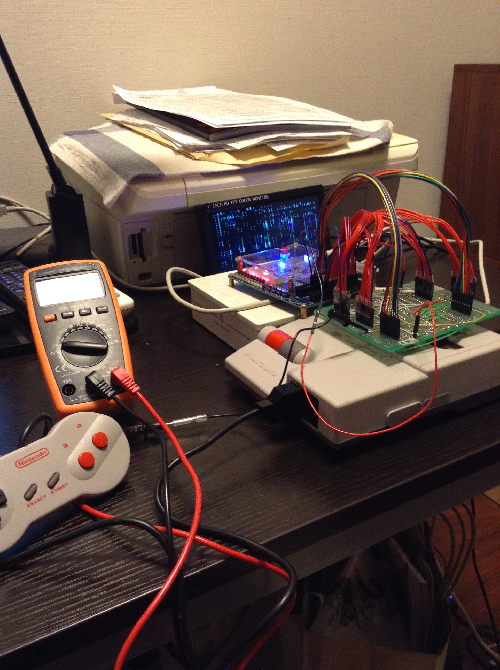
doc/craft-work-diary/20170416/IMG_0029.JPG
