astoria-d/super-duper-nes/doc/craft-work-diary/20170422/IMG_0031.JPG

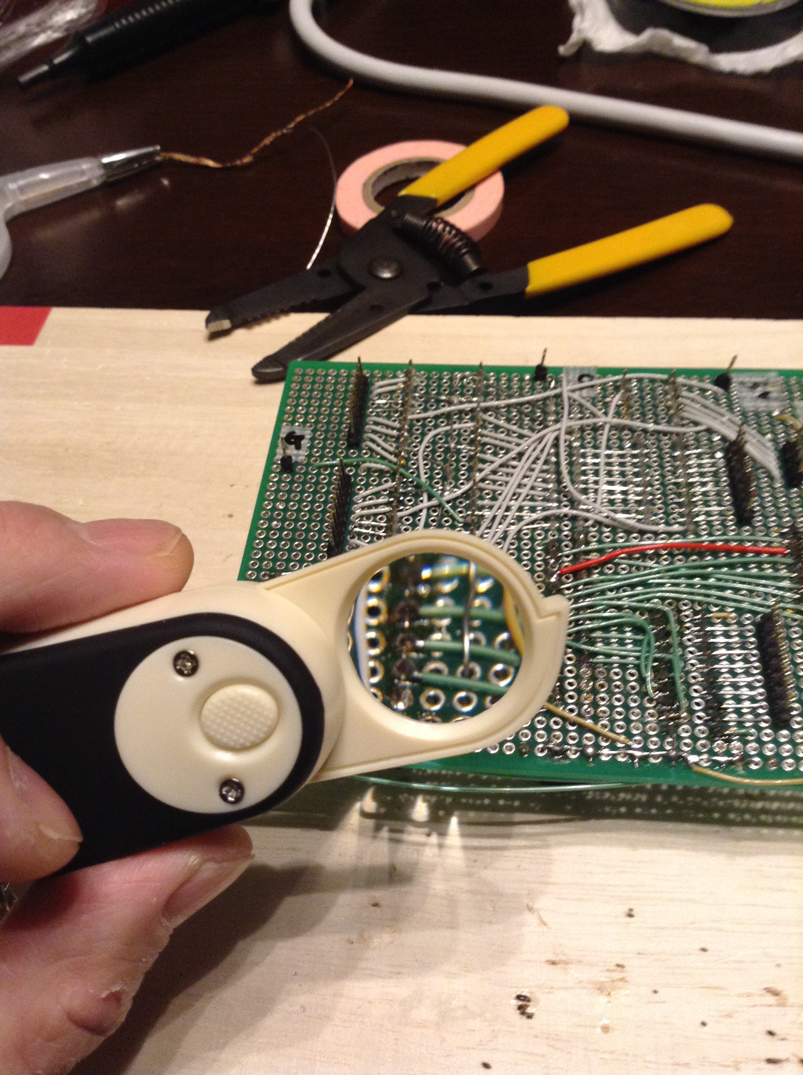
doc/craft-work-diary/20170422/IMG_0031.JPG
