astoria-d/super-duper-nes/doc/craft-work-diary/20170423/IMG_0033.JPG

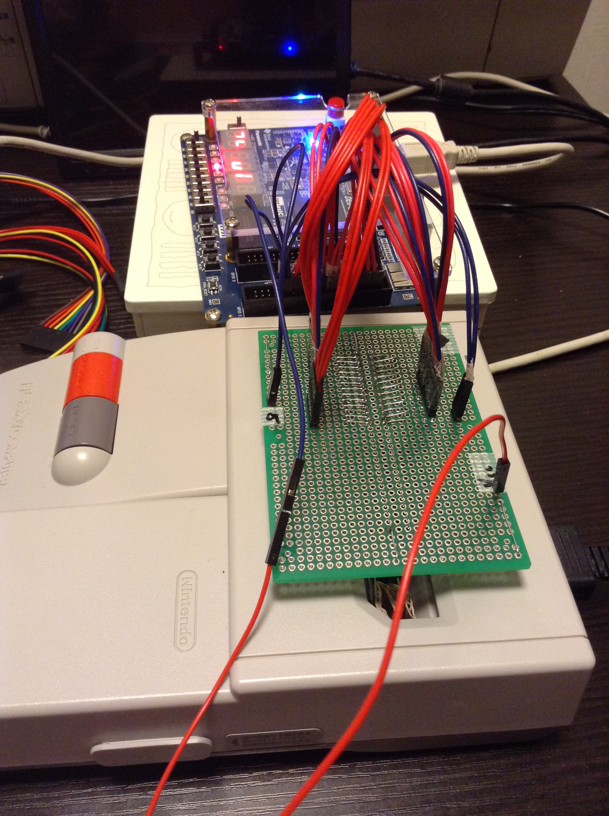
doc/craft-work-diary/20170423/IMG_0033.JPG
