astoria-d/super-duper-nes/doc/craft-work-diary/20170423/IMG_0036.JPG

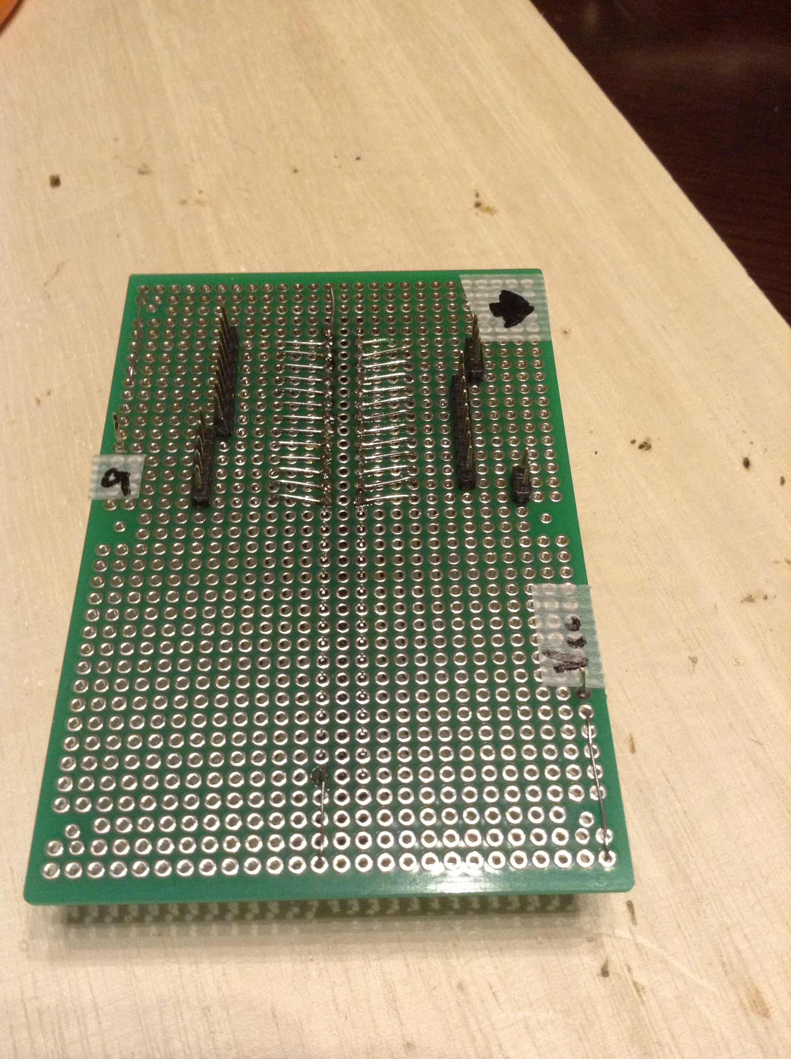
doc/craft-work-diary/20170423/IMG_0036.JPG
