astoria-d/super-duper-nes/doc/craft-work-diary/20170430/IMG_0041.JPG

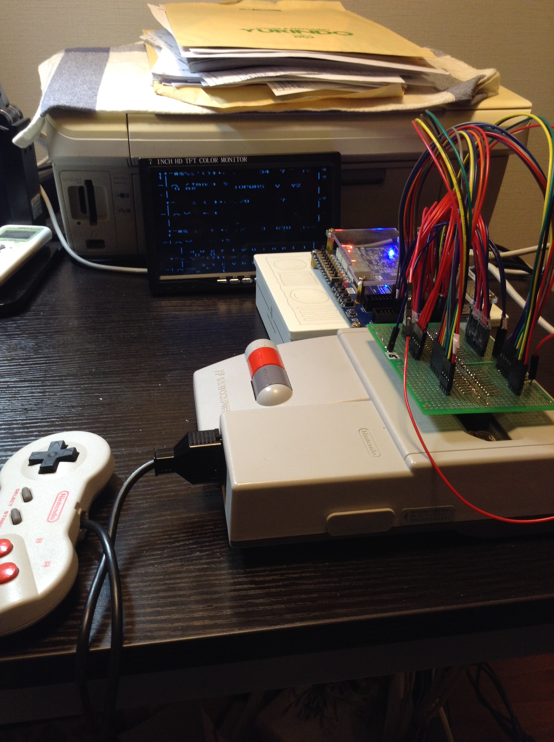
doc/craft-work-diary/20170430/IMG_0041.JPG
