astoria-d/super-duper-nes/doc/craft-work-diary/20170501/IMG_0046.JPG

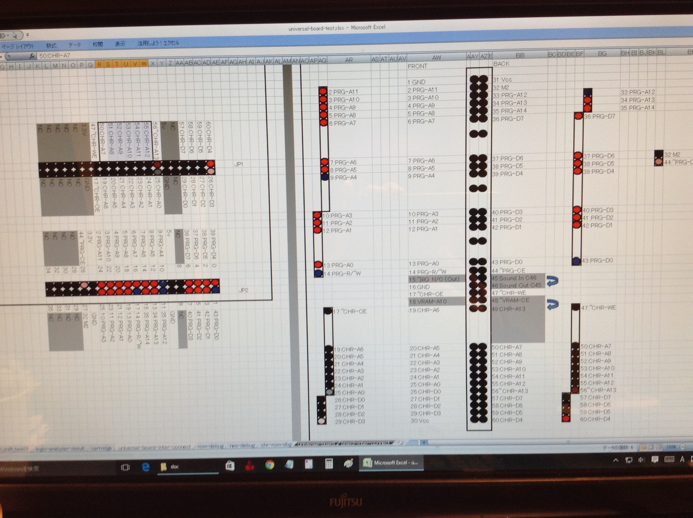
doc/craft-work-diary/20170501/IMG_0046.JPG
