astoria-d/super-duper-nes/doc/craft-work-diary/20170514/IMG_0059.JPG

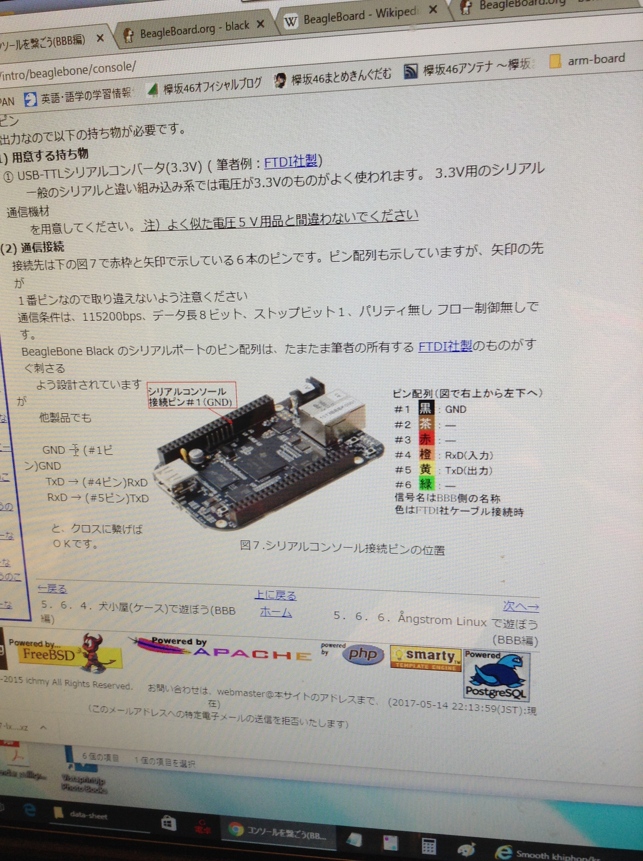
doc/craft-work-diary/20170514/IMG_0059.JPG
