astoria-d/super-duper-nes/doc/craft-work-diary/20170520/IMG_0061.JPG

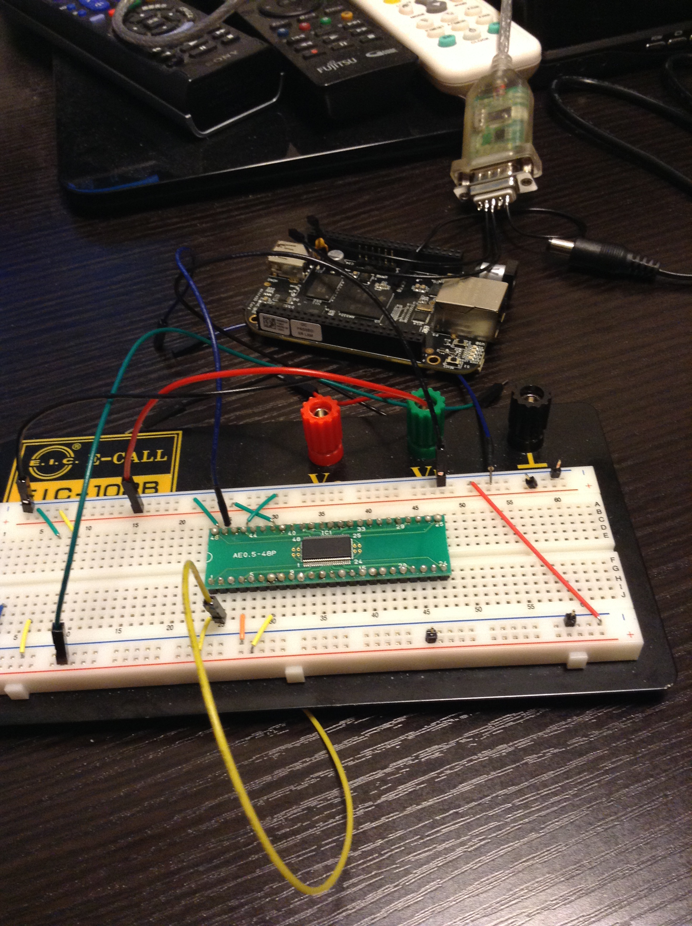
doc/craft-work-diary/20170520/IMG_0061.JPG
