astoria-d/super-duper-nes/doc/craft-work-diary/20170528/IMG_0065.JPG

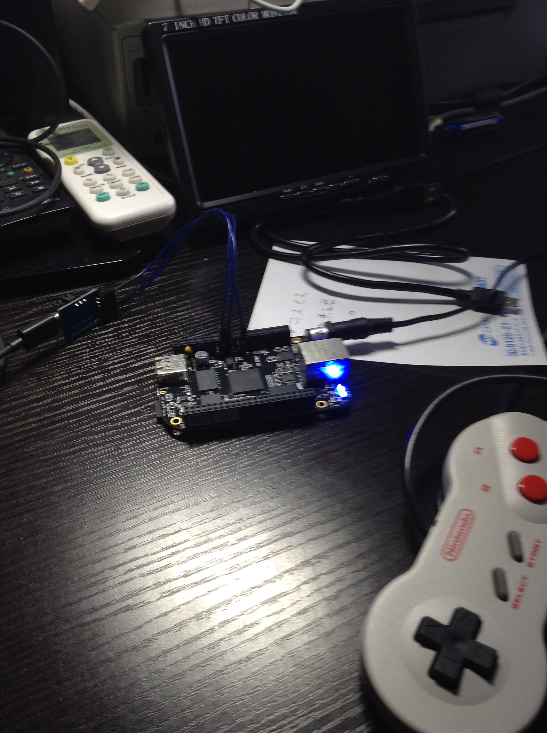
doc/craft-work-diary/20170528/IMG_0065.JPG
