astoria-d/super-duper-nes/doc/craft-work-diary/20170706/IMG_0066.JPG

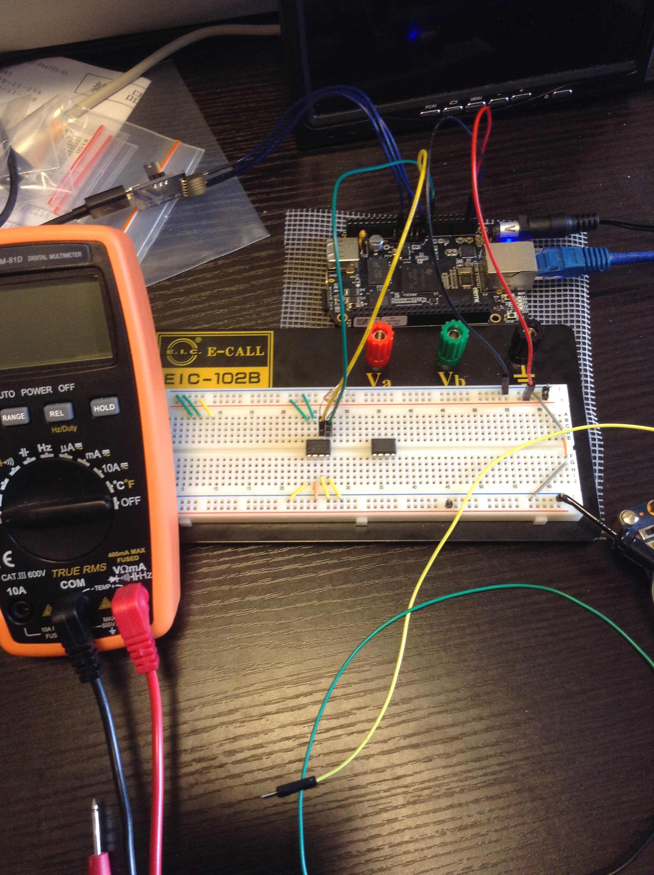
doc/craft-work-diary/20170706/IMG_0066.JPG
