astoria-d/super-duper-nes/doc/craft-work-diary/20170708/IMG_0067.JPG

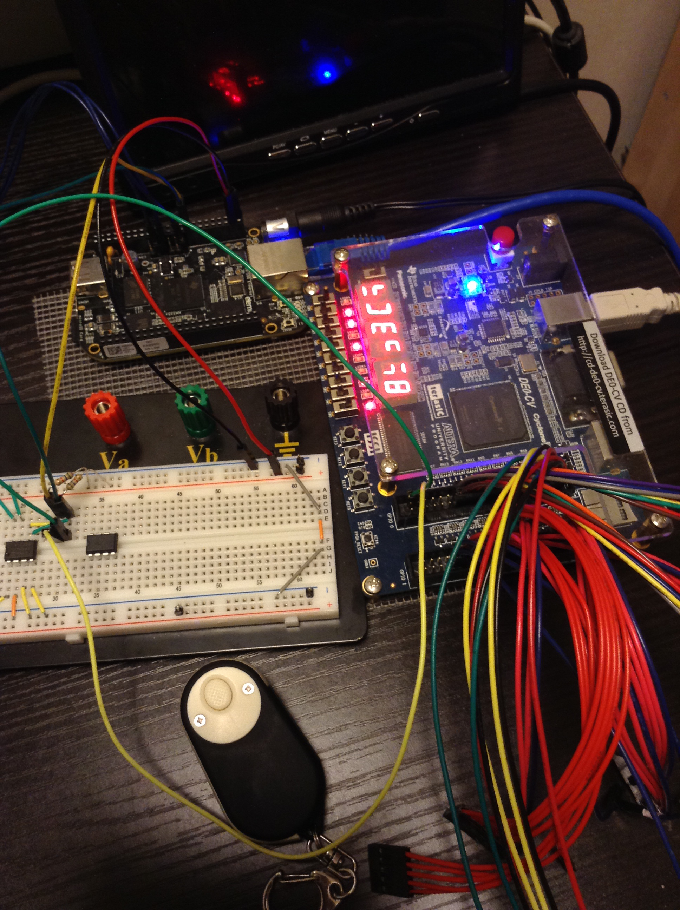
doc/craft-work-diary/20170708/IMG_0067.JPG
