astoria-d/super-duper-nes/doc/craft-work-diary/20170708/IMG_0068.JPG

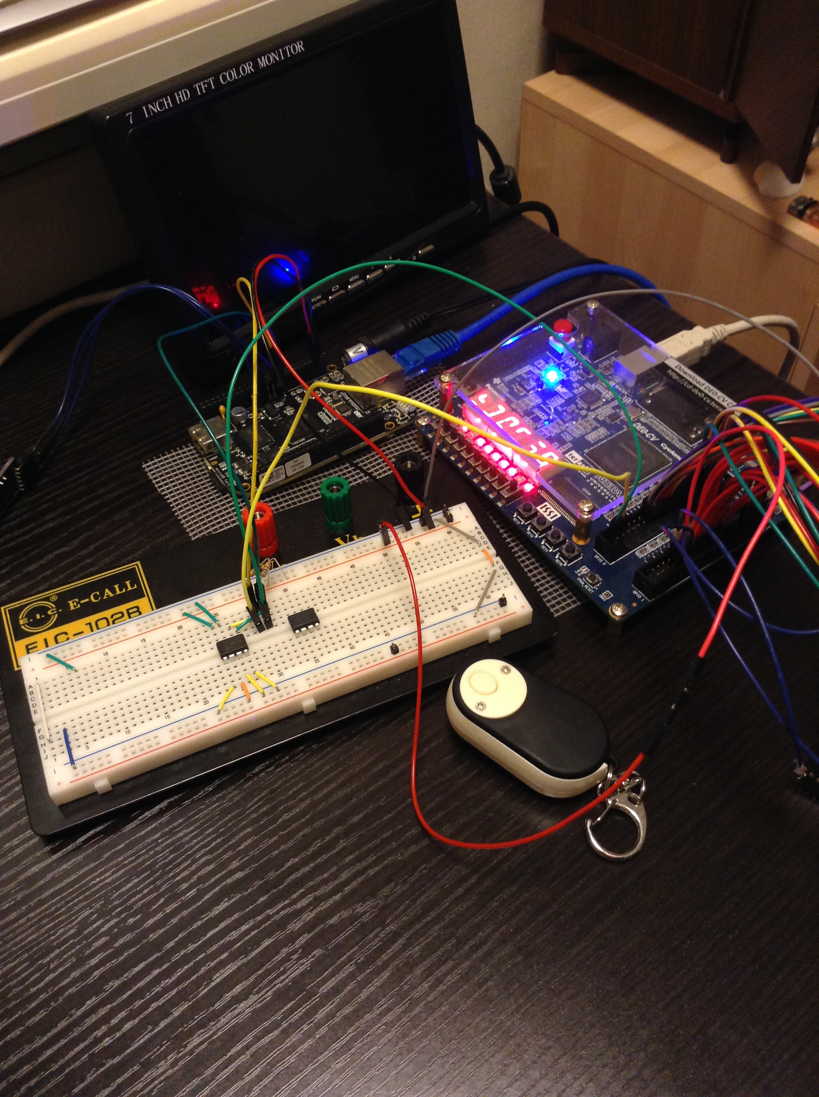
doc/craft-work-diary/20170708/IMG_0068.JPG
