astoria-d/super-duper-nes/doc/craft-work-diary/20170903/IMG_0074.JPG

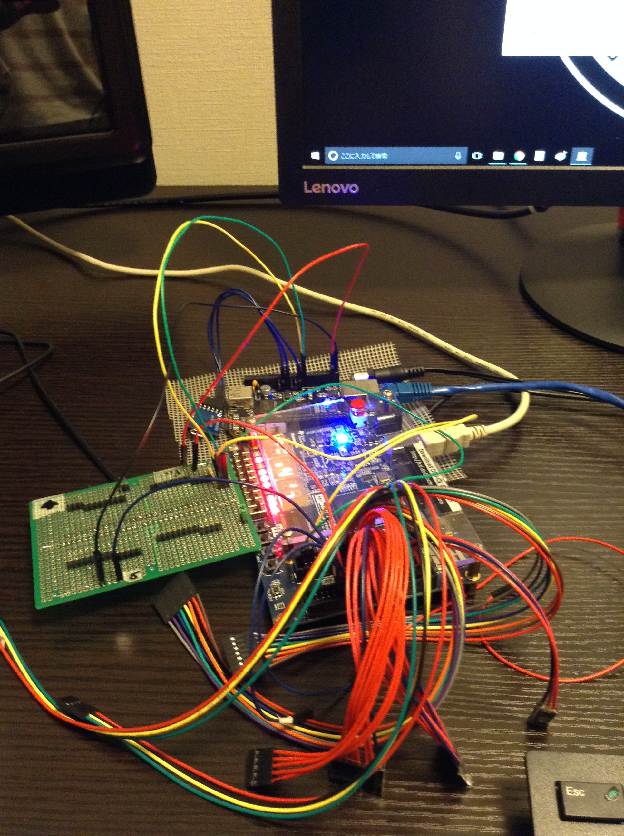
doc/craft-work-diary/20170903/IMG_0074.JPG
