astoria-d/super-duper-nes/doc/craft-work-diary/20170903/IMG_0078.JPG

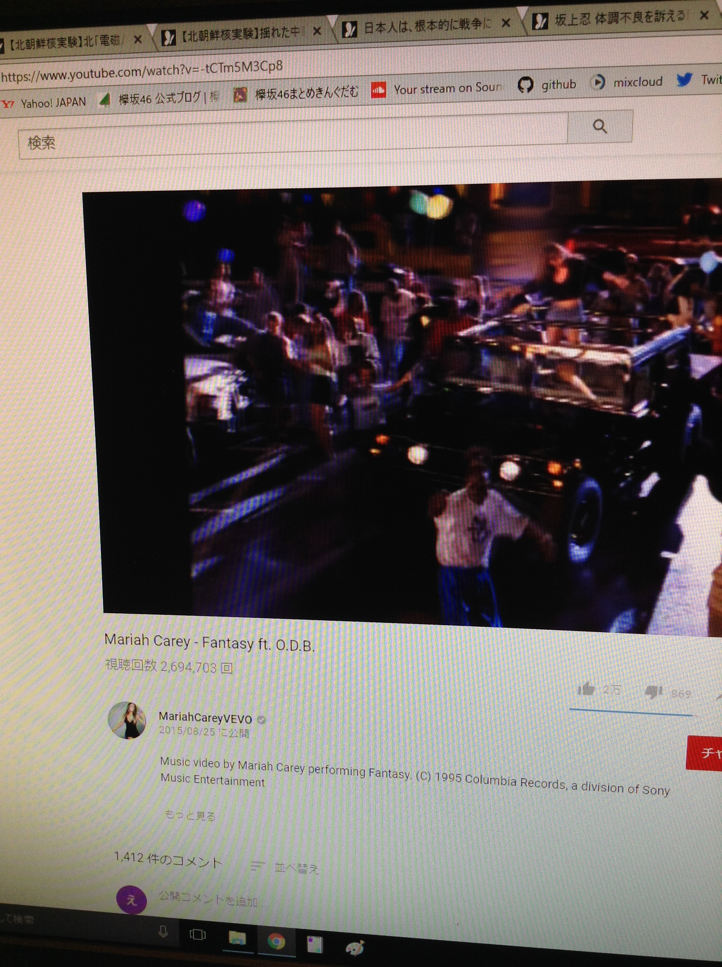
doc/craft-work-diary/20170903/IMG_0078.JPG
