astoria-d/super-duper-nes/doc/craft-work-diary/20170910/IMG_0079.JPG

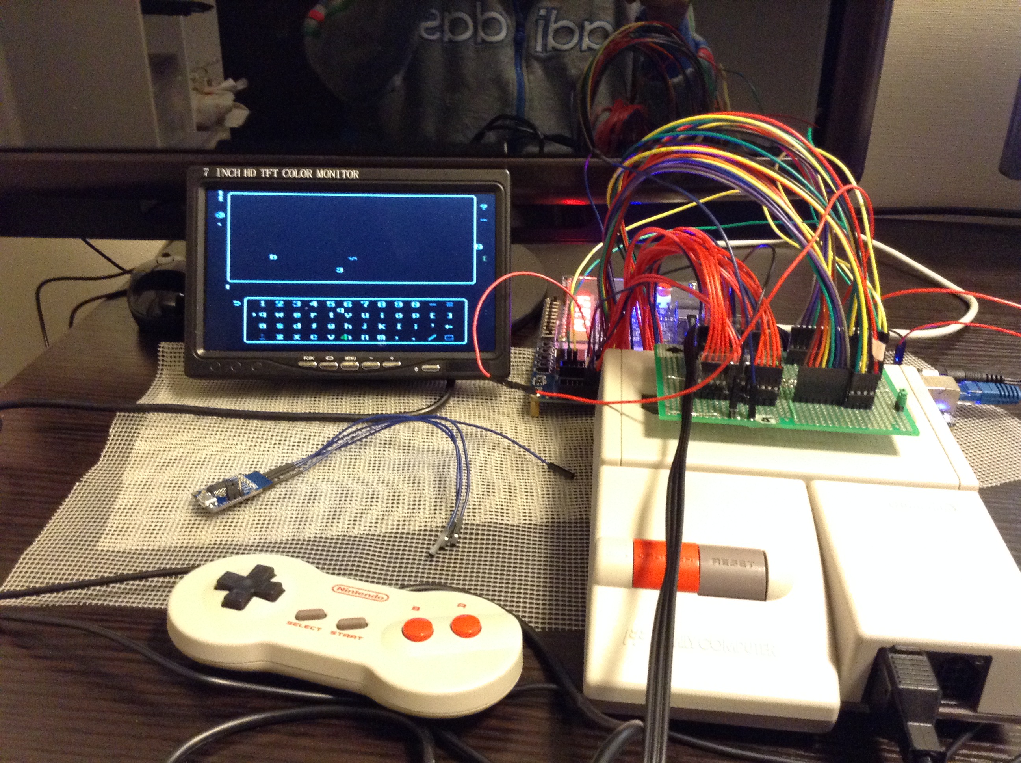
doc/craft-work-diary/20170910/IMG_0079.JPG
