astoria-d/super-duper-nes/doc/craft-work-diary/20171216/IMG_0086.JPG

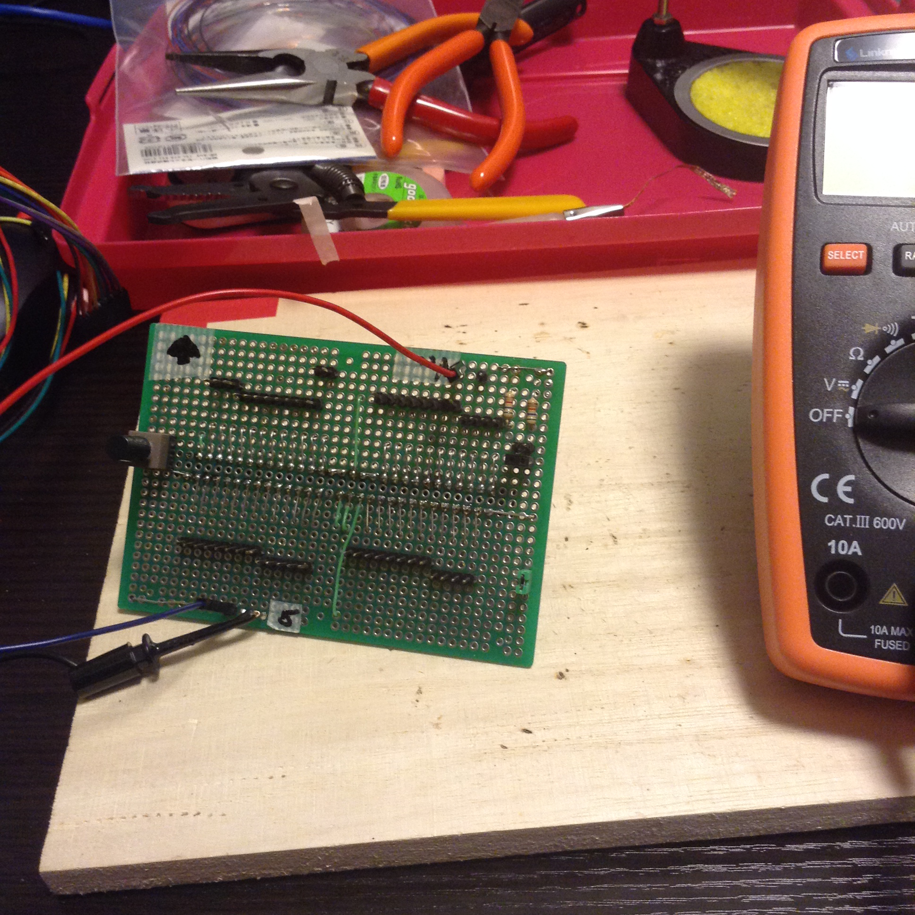
doc/craft-work-diary/20171216/IMG_0086.JPG
