astoria-d/super-duper-nes/doc/craft-work-diary/20171224/IMG_0090.JPG

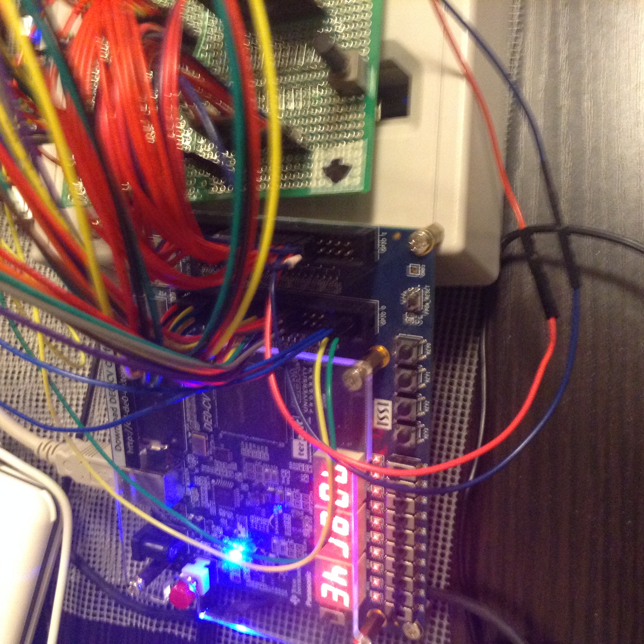
doc/craft-work-diary/20171224/IMG_0090.JPG
