astoria-d/super-duper-nes/doc/craft-work-diary/20180107/IMG_0092.JPG

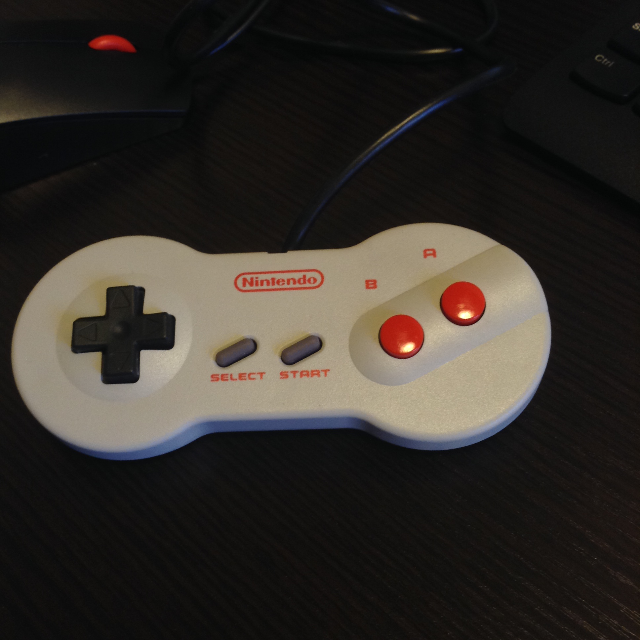
doc/craft-work-diary/20180107/IMG_0092.JPG
