astoria-d/super-duper-nes/doc/craft-work-diary/20180107/IMG_0093.JPG

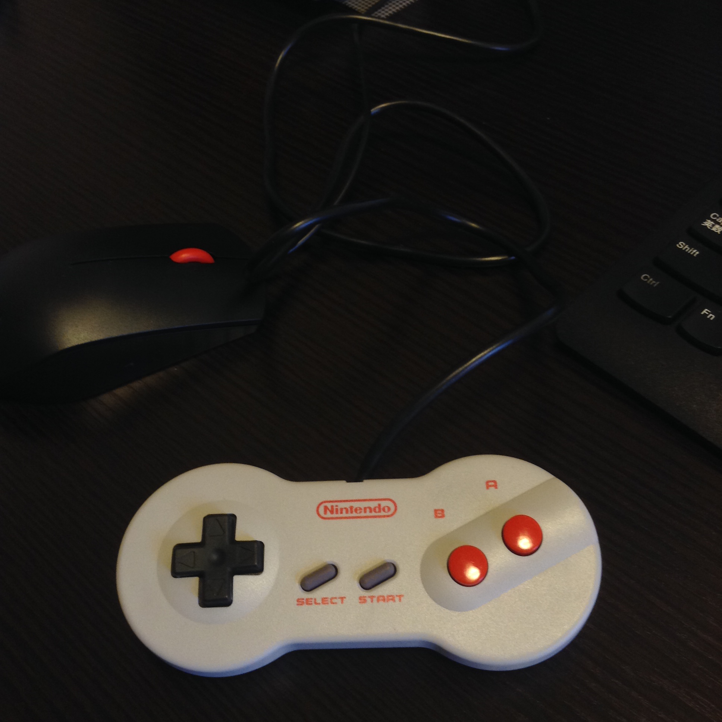
doc/craft-work-diary/20180107/IMG_0093.JPG
