astoria-d/super-duper-nes/doc/craft-work-diary/20180107/IMG_0094.JPG

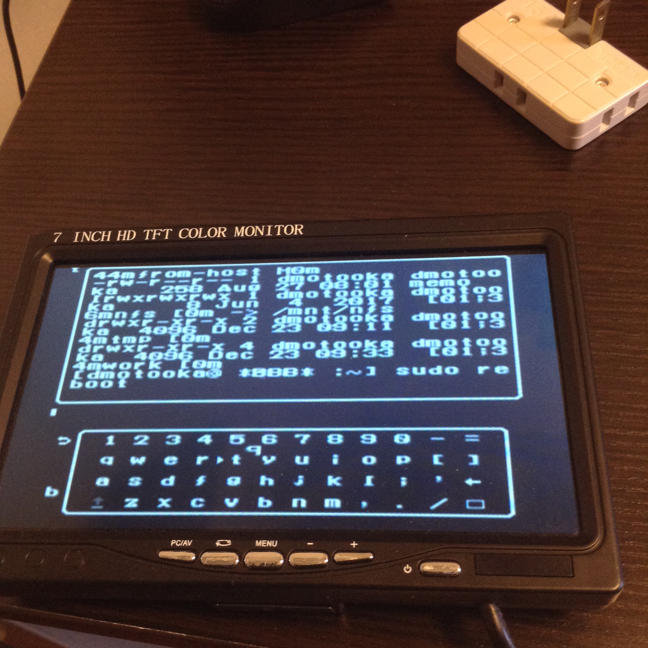
doc/craft-work-diary/20180107/IMG_0094.JPG
