astoria-d/super-duper-nes/circuit-diagram/bread-board-5to33-test03.asc

R1: res; 10k
vcc5: voltage; PULSE(0 5 200ms 100ms 100ms 300ms 1s)
Named nets: fpga-gpio-in-port, 0
.tran 1s
