astoria-d/super-duper-nes/circuit-diagram/de0-cv-gpio-test2.asc

D1: schottky; BAT54
D3: schottky; BAT54
gpio_input_pin: voltage; PULSE(0v 5v 0 0 0 1ms 2ms)
R1: res; 33
vcc3p3: voltage; 3.3v
Named nets: 0, fpga_input_pin
.tran 10ms
