astoria-d/super-duper-nes/circuit-diagram/de0-cv-gpio-test.asc

D1: schottky
D2: schottky
gpio_input1: voltage; PULSE(0v 5v 0 0 0 1ms 2ms)
R1: res; 33
vcc: voltage; 3.3v
Named nets: 0, fpga_pin
.tran 10ms
