astoria-d/super-duper-nes/circuit-diagram/nes-cirtridge-if.asc

V1: voltage; 5
V2: voltage; 5
V3: voltage; 3
Named nets: CPU_A11, CPU_A10, CPU_A09, CPU_A08, CPU_A07, CPU_A06, CPU_A05, CPU_A04, CPU_A03, CPU_A02, CPU_A01, CPU_A00, CPU_RW, /IRQ, 0, CIRAM_A10, /PPU_RD, PPU_A06, PPU_A05, PPU_A04, PPU_A03, PPU_A02, PPU_A01, PPU_A00, PPU_D00, PPU_D01, PPU_D02, PPU_D03, CPU_D07, CPU_A12, CPU_A13, CPU_A14, CPU_D06, CPU_D05, CPU_D04, CPU_D03, CPU_D02, CPU_D01, CPU_D00, /ROMSEL, Audio_IN, Audio_OUT, /PPU_WR, /CIRAM_CE, /PPU_A13, PPU_A07, PPU_A08, PPU_A09, PPU_A10, PPU_A11, PPU_A12, PPU_A13, PPU_D07, PPU_D06, PPU_D05, PPU_D04, GPIO_0_D00, GPIO_0_D02, GPIO_0_D04, GPIO_0_D06, GPIO_0_D08, GPIO_0_D10, GPIO_0_D12, GPIO_0_D14, GPIO_0_D16, GPIO_0_D18, GPIO_0_D20, GPIO_0_D22, GPIO_0_D24, GPIO_0_D26, GPIO_0_D28, GPIO_0_D30, GPIO_0_D32, GPIO_0_D34, GPIO_0_D01, GPIO_0_D03, GPIO_0_D05, GPIO_0_D07, GPIO_0_D09, GPIO_0_D11, GPIO_0_D13, GPIO_0_D15, GPIO_0_D17, GPIO_0_D19, GPIO_0_D21, GPIO_0_D23, GPIO_0_D25, GPIO_0_D27, GPIO_0_D29, GPIO_0_D31, GPIO_0_D33, GPIO_0_D35, GPIO_1_D00, GPIO_1_D02, GPIO_1_D04, GPIO_1_D06, GPIO_1_D08, GPIO_1_D10, GPIO_1_D12, GPIO_1_D14, GPIO_1_D16, GPIO_1_D18, GPIO_1_D20, GPIO_1_D22, GPIO_1_D24, GPIO_1_D26, GPIO_1_D28, GPIO_1_D30, GPIO_1_D32, GPIO_1_D34, GPIO_1_D01, GPIO_1_D03, GPIO_1_D05, GPIO_1_D07, GPIO_1_D09, GPIO_1_D11, GPIO_1_D13, GPIO_1_D15, GPIO_1_D17, GPIO_1_D19, GPIO_1_D21, GPIO_1_D23, GPIO_1_D25, GPIO_1_D27, GPIO_1_D29, GPIO_1_D31, GPIO_1_D33, GPIO_1_D35, GND, +5, M2, +3
NES frontside
NES backside
GPIO 1: front
GPIO 1 back
GPIO 2 front
GPIO 2 back
.tran 10ms
