astoria-d/super-duper-nes/duper_cartridge/duper_cartridge.vhd

library ieee;
use ieee.std_logic_1164.all;
use ieee.std_logic_unsigned.conv_integer;
use ieee.std_logic_arith.conv_std_logic_vector;
use ieee.std_logic_unsigned.all;

--entity rom_test01 is 
entity duper_cartridge is 
    port (
        pi_reset_n      : in std_logic;
        pi_base_clk     : in std_logic;

        --nes side
        pi_phi2             : in std_logic;

        --prgrom
        pi_prg_ce_n         : in std_logic;
        pi_prg_r_nw         : in std_logic;
        pi_prg_addr         : in std_logic_vector(14 downto 0);
        pio_prg_data        : inout std_logic_vector(7 downto 0);

        --chrrom
        pi_chr_ce_n         : in std_logic;
        pi_chr_oe_n         : in std_logic;
        pi_chr_we_n         : in std_logic;
        pi_chr_addr         : in std_logic_vector(12 downto 0);
        po_chr_data         : out std_logic_vector(7 downto 0);

        --i2c side
        pi_i2c_scl      : in    std_logic;
        pio_i2c_sda     : inout std_logic;

        --bbb gpio
        po_nes_f_full   : out   std_logic;
        po_bbb_f_empty  : out   std_logic;

        po_dbg_cnt          : out std_logic_vector (63 downto 0)
        );
--end rom_test01;
end duper_cartridge;

--architecture rtl of rom_test01 is
architecture rtl of duper_cartridge is

-------------------------------------------
-------------------------------------------
------------- definitions.... -------------
-------------------------------------------
-------------------------------------------

component synchronizer port (
    pi_rst_n            : in    std_logic;
    pi_base_clk         : in    std_logic;
    pi_async_input      : in    std_logic;
    po_sync_output      : out   std_logic
    );
end component;

component synchronized_vector
    generic (abus_size : integer := 8);
    port (
        pi_rst_n            : in    std_logic;
        pi_base_clk         : in    std_logic;
        pi_async_input      : in    std_logic_vector(abus_size - 1 downto 0);
        po_sync_output      : out   std_logic_vector(abus_size - 1 downto 0)
    );
end component;

component prg_rom port (
    pi_base_clk     : in std_logic;
    pi_ce_n         : in std_logic;
    pi_oe_n         : in std_logic;
    pi_addr         : in std_logic_vector (14 downto 0);
    po_data         : out std_logic_vector (7 downto 0)
    );
end component ;

component chr_rom port (
    pi_base_clk 	: in std_logic;
    pi_ce_n         : in std_logic;
    pi_oe_n         : in std_logic;
    pi_addr         : in std_logic_vector (12 downto 0);
    po_data         : out std_logic_vector (7 downto 0)
    );
end component;

component i2c_slave
port (
    pi_rst_n            : in    std_logic;
    pi_base_clk         : in    std_logic;
    ---i2c bus lines...
    pi_slave_addr       : in    std_logic_vector (6 downto 0);
    pi_i2c_scl          : in    std_logic;
    pi_i2c_sda          : in    std_logic;
    po_i2c_sda          : out   std_logic;
    ---i2c bus contoler internal lines...
    pi_i2c_read_data    : in    std_logic_vector (7 downto 0);
    po_i2c_write_data   : out   std_logic_vector (7 downto 0);
    po_i2c_status       : out   std_logic_vector (3 downto 0)
    );
end component;

component fifo
    generic (abus_size : integer := 8);
    port (
        pi_rst_n        : in std_logic;
        pi_base_clk     : in std_logic;
        pi_ce_n         : in std_logic;
        pi_oe_n         : in std_logic;
        pi_push_n       : in std_logic;
        pi_pop_n        : in std_logic;
        pi_data         : in std_logic_vector (7 downto 0);
        po_data         : out std_logic_vector (7 downto 0);
        po_stat_empty   : out std_logic;
        po_stat_full    : out std_logic
    );
end component;

---fifo status register
---bit	
---7	always 0
---6	always 0
---5	read fifo full
---4	read fifo empty
---3	always 0
---2	always 0
---1	write fifo full
---0	write fifo empty
constant wfifo_empty_bit    : integer := 0;
constant wfifo_full_bit     : integer := 1;
constant rfifo_empty_bit    : integer := 4;
constant rfifo_full_bit     : integer := 5;


type duper_state_machine is (
    idle,
    rom_read,
    rom_read_ok,
    fifo_status_read,
    nes_fifo_read,
    nes_fifo_pop,
    nes_fifo_read_ok,
    nes_fifo_write,
    nes_fifo_push,
    nes_fifo_write_ok,
    bbb_fifo_read,
    bbb_fifo_pop,
    bbb_fifo_read_ok,
    bbb_fifo_write,
    bbb_fifo_push,
    bbb_fifo_write_ok
    );

constant DATA_DELAY     : integer := 18;

-------------------------------------------
-------------------------------------------
------------- declarations... -------------
-------------------------------------------
-------------------------------------------

--synchronized input.
--nes side
--signal reg_phi2             : std_logic;
signal reg_prg_ce_n         : std_logic;
signal reg_prg_r_nw         : std_logic;
signal reg_prg_addr         : std_logic_vector(14 downto 0);
signal reg_prg_data_in      : std_logic_vector(7 downto 0);
signal reg_chr_ce_n         : std_logic;
signal reg_chr_oe_n         : std_logic;
--signal reg_chr_we_n         : std_logic;
signal reg_chr_addr         : std_logic_vector(12 downto 0);
--bbb side
signal reg_i2c_scl          : std_logic;
signal reg_i2c_sda_in       : std_logic;

signal wr_prg_data_out      : std_logic_vector(7 downto 0);
signal reg_prg_data_out     : std_logic_vector(7 downto 0);

--duper state machine..
signal reg_cur_state        : duper_state_machine;
signal reg_next_state       : duper_state_machine;
signal reg_delay_cnt        : integer range 0 to 31;


--prgrom reg
signal reg_prom_oe_n        : std_logic;

--read fifo registers.
signal reg_ififo_ce_n        : std_logic;
signal reg_ififo_oe_n        : std_logic;
signal reg_ififo_push_n      : std_logic;
signal reg_ififo_pop_n       : std_logic;
signal reg_ififo_status      : std_logic_vector (7 downto 0);

signal wr_ififo_empty       : std_logic;
signal wr_ififo_full        : std_logic;
signal wr_ififo_data        : std_logic_vector (7 downto 0);

--write fifo registers.
signal reg_ofifo_ce_n       : std_logic;
signal reg_ofifo_oe_n       : std_logic;
signal reg_ofifo_push_n     : std_logic;
signal reg_ofifo_pop_n      : std_logic;
signal reg_ofifo_status     : std_logic_vector (7 downto 0);

signal wr_ofifo_empty       : std_logic;
signal wr_ofifo_full        : std_logic;
signal wr_ofifo_data        : std_logic_vector (7 downto 0);

--i2c registers.
signal wr_i2c_sda_out       : std_logic;
signal wr_i2c_in_data       : std_logic_vector (7 downto 0);
signal reg_i2c_rd_done      : integer range 0 to 1;
signal reg_i2c_wr_done      : integer range 0 to 1;


---po_i2c_status(3): '1' = bus transfering, '0' = stopped.
---po_i2c_status(2): '1' = read, '0' = write.
---po_i2c_status(1): '1' = data acknowleged, '0' = not acknowleged.
---po_i2c_status(0): '1' = addr acknowleged, '0' = not acknowleged.
signal wr_i2c_status     : std_logic_vector (3 downto 0);

------------misc regs.
signal reg_dbg_cnt      : std_logic_vector (63 downto 0);

-------------------------------------------
-------------------------------------------
------------ implementations... -----------
-------------------------------------------
-------------------------------------------


begin

    --async input to be aligned to the base clock...
--    sync00 : synchronizer port map (pi_reset_n, pi_base_clk, pi_phi2,        reg_phi2);
    sync01 : synchronizer port map (pi_reset_n, pi_base_clk, pi_prg_ce_n,    reg_prg_ce_n);
    sync02 : synchronizer port map (pi_reset_n, pi_base_clk, pi_prg_r_nw,    reg_prg_r_nw);
    sync03 : synchronizer port map (pi_reset_n, pi_base_clk, pi_chr_ce_n,    reg_chr_ce_n);
    sync04 : synchronizer port map (pi_reset_n, pi_base_clk, pi_chr_oe_n,    reg_chr_oe_n);
--    sync05 : synchronizer port map (pi_reset_n, pi_base_clk, pi_chr_we_n,    reg_chr_we_n);
    sync06 : synchronizer port map (pi_reset_n, pi_base_clk, pi_i2c_scl,     reg_i2c_scl);
    sync07 : synchronizer port map (pi_reset_n, pi_base_clk, pio_i2c_sda,    reg_i2c_sda_in);

    sync10 : synchronized_vector generic map (15)    port map (pi_reset_n, pi_base_clk, pi_prg_addr,    reg_prg_addr);
    sync11 : synchronized_vector generic map (8)     port map (pi_reset_n, pi_base_clk, pio_prg_data,   reg_prg_data_in);
    sync12 : synchronized_vector generic map (13)    port map (pi_reset_n, pi_base_clk, pi_chr_addr,    reg_chr_addr);

    --base clock synchronized registers...
    reg_p : process (pi_base_clk, pi_reset_n)
    begin
        if (pi_reset_n = '0') then
            reg_ififo_status <= "00010001";

        elsif (rising_edge(pi_base_clk)) then
            reg_ififo_status(7 downto 6) <= (others => '0');
            reg_ififo_status(rfifo_full_bit)     <= wr_ififo_full;
            reg_ififo_status(rfifo_empty_bit)    <= wr_ififo_empty;
            reg_ififo_status(3 downto 2) <= (others => '0');
            reg_ififo_status(wfifo_full_bit)     <= wr_ofifo_full;
            reg_ififo_status(wfifo_empty_bit)    <= wr_ofifo_empty;
        end if;
    end process;
    po_nes_f_full <= reg_ififo_status(rfifo_full_bit);
    po_bbb_f_empty <= reg_ififo_status(wfifo_empty_bit);

    --state transition process...
    set_stat_p : process (pi_reset_n, pi_base_clk)
    begin
        if (pi_reset_n = '0') then
            reg_cur_state <= idle;
        elsif (rising_edge(pi_base_clk)) then
            reg_cur_state <= reg_next_state;
        end if;--if (pi_rst_n = '0') then
    end process;

    --cpu data wait proc...
    delay_cnt_p : process (pi_reset_n, pi_base_clk)
    begin
        if (pi_reset_n = '0') then
            reg_delay_cnt <= 0;
        elsif (rising_edge(pi_base_clk)) then
            if (reg_cur_state = bbb_fifo_write) then
                reg_delay_cnt <= reg_delay_cnt + 1;
            else
                reg_delay_cnt <= 0;
            end if;
        end if;--if (pi_rst_n = '0') then
    end process;

    --state change to next.
    vac_next_stat_p : process (reg_cur_state, reg_prg_ce_n, reg_prg_r_nw, reg_prg_addr, wr_i2c_status, 
                               reg_i2c_rd_done, reg_i2c_wr_done, reg_delay_cnt)
    begin
        case reg_cur_state is
            when idle =>
                --rom read 0x7ff9: fifo read.
                if (reg_prg_ce_n = '0' and reg_prg_r_nw = '1' and reg_prg_addr = "111111111111001") then
                    reg_next_state <= nes_fifo_read;

                --rom write 0x7ff9: fifo write.
                elsif (reg_prg_ce_n = '0' and reg_prg_r_nw = '0' and reg_prg_addr = "111111111111001") then
                    reg_next_state <= bbb_fifo_write;

                --rom read 0x7ff8: fifo status read.
                elsif (reg_prg_ce_n = '0' and reg_prg_r_nw = '1' and reg_prg_addr = "111111111111000") then
                    reg_next_state <= fifo_status_read;

                --other rom read.
                elsif (reg_prg_ce_n = '0' and reg_prg_r_nw = '1') then
                    reg_next_state <= rom_read;

                else
                --no rom access...

---po_i2c_status(3): '1' = bus transfering, '0' = stopped.
---po_i2c_status(2): '1' = read, '0' = write.
---po_i2c_status(1): '1' = data acknowleged, '0' = not acknowleged.
---po_i2c_status(0): '1' = addr acknowleged, '0' = not acknowleged.

                    if (wr_i2c_status(1) = '1' and wr_i2c_status(2) = '0') then
                    --case bbb push fifo.
                        if (reg_i2c_wr_done = 0) then
                            reg_next_state <= nes_fifo_write;
                        else
                            reg_next_state <= idle;
                        end if;

                    elsif (wr_i2c_status(1) = '1' and wr_i2c_status(2) = '1') then
                    --case bbb pop fifo.
                        if (reg_i2c_rd_done = 0) then
                            reg_next_state <= bbb_fifo_read;
                        else
                            reg_next_state <= idle;
                        end if;

                    else
                        reg_next_state <= idle;
                    end if;
                end if;

            when rom_read =>
                reg_next_state <= rom_read_ok;

            when rom_read_ok =>
                if (reg_prg_ce_n = '0' and reg_prg_r_nw = '1' and reg_prg_addr(14 downto 1) /= "11111111111100") then
                    reg_next_state <= rom_read_ok;
                else
                    reg_next_state <= idle;
                end if;

            when fifo_status_read =>
                if (reg_prg_ce_n = '0' and reg_prg_r_nw = '1' and reg_prg_addr = "111111111111000") then
                    reg_next_state <= fifo_status_read;
                else
                    reg_next_state <= idle;
                end if;

            when nes_fifo_read =>
                reg_next_state <= nes_fifo_pop;

            when nes_fifo_pop =>
                reg_next_state <= nes_fifo_read_ok;

            when nes_fifo_read_ok =>
                if (reg_prg_ce_n = '0' and reg_prg_r_nw = '1' and reg_prg_addr = "111111111111001") then
                    reg_next_state <= nes_fifo_read_ok;
                else
                    reg_next_state <= idle;
                end if;

            when nes_fifo_write =>
                reg_next_state <= nes_fifo_push;

            when nes_fifo_push =>
                reg_next_state <= nes_fifo_write_ok;

            when nes_fifo_write_ok =>
                reg_next_state <= idle;

            when bbb_fifo_read =>
                reg_next_state <= bbb_fifo_pop;

            when bbb_fifo_pop =>
                reg_next_state <= bbb_fifo_read_ok;

            when bbb_fifo_read_ok =>
                reg_next_state <= idle;

            when bbb_fifo_write =>
                if (reg_delay_cnt < DATA_DELAY) then
                    --wait for data to be available.
                    reg_next_state <= bbb_fifo_write;
                else
                    reg_next_state <= bbb_fifo_push;
                end if;

            when bbb_fifo_push =>
                reg_next_state <= bbb_fifo_write_ok;

            when bbb_fifo_write_ok =>
                if (reg_prg_ce_n = '0' and reg_prg_r_nw = '0' and reg_prg_addr = "111111111111001") then
                    reg_next_state <= bbb_fifo_write_ok;
                else
                    reg_next_state <= idle;
                end if;


        end case;
    end process;

    push_handle_p : process (pi_reset_n, pi_base_clk)
    begin
        if (pi_reset_n = '0') then
            reg_i2c_rd_done <= 0;
            reg_i2c_wr_done <= 0;
        elsif (rising_edge(pi_base_clk)) then
            if (wr_i2c_status(1) = '0') then
                reg_i2c_wr_done <= 0;
            elsif (reg_cur_state = nes_fifo_push) then
                reg_i2c_wr_done <= 1;
            end if;

---po_i2c_status(3): '1' = bus transfering, '0' = stopped.
---po_i2c_status(2): '1' = read, '0' = write.
---po_i2c_status(1): '1' = data acknowleged, '0' = not acknowleged.
---po_i2c_status(0): '1' = addr acknowleged, '0' = not acknowleged.
            if (reg_cur_state = bbb_fifo_pop) then
                reg_i2c_rd_done <= 1;
            elsif (reg_cur_state = idle and (wr_i2c_status(1) = '0')) then
                reg_i2c_rd_done <= 0;
            end if;

        end if;--if (pi_rst_n = '0') then
    end process;


    --each register setting..
    regs_p : process (pi_reset_n, pi_base_clk)
    begin
        if (pi_reset_n = '0') then
            reg_prom_oe_n <= '1';
            reg_ififo_ce_n <= '1';
            reg_ififo_oe_n <= '1';
            reg_ififo_push_n <= '1';
            reg_ififo_pop_n <= '1';
            reg_ofifo_ce_n <= '1';
            reg_ofifo_oe_n <= '1';
            reg_ofifo_push_n <= '1';
            reg_ofifo_pop_n <= '1';
        elsif (rising_edge(pi_base_clk)) then
            case reg_cur_state is
                when idle =>
                    reg_prom_oe_n <= '0';
                    reg_ififo_ce_n <= '0';
                    reg_ififo_oe_n <= '0';
                    reg_ififo_push_n <= '1';
                    reg_ififo_pop_n <= '1';

                    reg_ofifo_ce_n <= '0';
                    reg_ofifo_oe_n <= '0';
                    reg_ofifo_push_n <= '1';
                    reg_ofifo_pop_n <= '1';

                when rom_read =>

                when rom_read_ok =>

                when fifo_status_read =>

                when nes_fifo_read =>
                    reg_ififo_pop_n <= '1';

                when nes_fifo_pop =>
                    reg_ififo_pop_n <= '0';

                when nes_fifo_read_ok =>
                    reg_ififo_pop_n <= '1';

                when nes_fifo_write =>
                    reg_ififo_push_n <= '1';

                when nes_fifo_push =>
                    reg_ififo_push_n <= '0';

                when nes_fifo_write_ok =>
                    reg_ififo_push_n <= '1';

                when bbb_fifo_read =>
                    reg_ofifo_pop_n <= '1';

                when bbb_fifo_pop =>
                    reg_ofifo_pop_n <= '0';

                when bbb_fifo_read_ok =>
                    reg_ofifo_pop_n <= '1';

                when bbb_fifo_write =>
                    reg_ofifo_push_n <= '1';

                when bbb_fifo_push =>
                    reg_ofifo_push_n <= '0';

                when bbb_fifo_write_ok =>
                    reg_ofifo_push_n <= '1';

            end case;
        end if;--if (pi_rst_n = '0') then
    end process;


    --prg rom
    pio_prg_data <= reg_prg_data_out;

    set_nes_out_p : process (pi_reset_n, pi_base_clk)
    variable tmp_fifo : std_logic_vector(7 downto 0);
    begin
        if (pi_reset_n = '0') then
            reg_prg_data_out <= (others => 'Z');
            tmp_fifo := (others => '0');
        elsif (rising_edge(pi_base_clk)) then
            case reg_cur_state is
                when rom_read_ok =>
                    reg_prg_data_out <= wr_prg_data_out;

                when fifo_status_read =>
                    reg_prg_data_out <= reg_ififo_status;

                when nes_fifo_read =>
                    reg_prg_data_out <= wr_ififo_data;
                    tmp_fifo := wr_ififo_data;

                when nes_fifo_pop =>
                    reg_prg_data_out <= tmp_fifo;

                when nes_fifo_read_ok =>
                    reg_prg_data_out <= tmp_fifo;

                when others =>
                    reg_prg_data_out <= (others => 'Z');
            end case;
        end if;--if (pi_rst_n = '0') then
    end process;

    prom_inst : prg_rom port map (
        pi_base_clk,
        reg_prg_ce_n,
        reg_prom_oe_n,
        reg_prg_addr,
        wr_prg_data_out
    );

    --i2c incoming fifo.
    rd_fifo_inst : fifo generic map (8)
    port map (
        pi_reset_n,
        pi_base_clk,
        reg_ififo_ce_n,
        reg_ififo_oe_n,
        reg_ififo_push_n,
        reg_ififo_pop_n,
        wr_i2c_in_data,
        wr_ififo_data,
        wr_ififo_empty,
        wr_ififo_full
    );

    --i2c outgoing fifo.
    wr_fifo_inst : fifo generic map (8)
    port map (
        pi_reset_n,
        pi_base_clk,
        reg_ofifo_ce_n,
        reg_ofifo_oe_n,
        reg_ofifo_push_n,
        reg_ofifo_pop_n,
        reg_prg_data_in,
        wr_ofifo_data,
        wr_ofifo_empty,
        wr_ofifo_full
    );

    --i2c slave
    i2c_slave_inst : i2c_slave
    port map (
        pi_reset_n,
        pi_base_clk,
        conv_std_logic_vector(16#44#, 7),
        reg_i2c_scl,
        reg_i2c_sda_in,
        wr_i2c_sda_out,
        wr_ofifo_data,
        wr_i2c_in_data,
        wr_i2c_status
    );
    pio_i2c_sda <= wr_i2c_sda_out;

    --character rom
    crom_inst : chr_rom port map (
        pi_base_clk, 
        reg_chr_ce_n,
        reg_chr_oe_n,
        reg_chr_addr, 
        po_chr_data
    );

----------------------------------------------------------------------
----------------------------------------------------------------------
-------------------------- misc processes.... ------------------------
----------------------------------------------------------------------
----------------------------------------------------------------------

    po_dbg_cnt <= reg_dbg_cnt;
    deb_cnt_p : process (pi_base_clk, pi_reset_n)
use ieee.std_logic_unsigned.all;
    begin
        if (pi_reset_n = '0') then
            reg_dbg_cnt <= (others => '0');
        elsif (rising_edge(pi_base_clk)) then
            reg_dbg_cnt <= reg_dbg_cnt + 1;
        end if;
    end process;
end rtl;
