astoria-d/super-duper-nes/duper_linux/bbb_tty/bt_module.c

#include <linux/init.h>
#include <linux/module.h>
#include <linux/kernel.h>

#include "bbb_tty.h"

MODULE_LICENSE("GPL");
MODULE_AUTHOR("astoria-d");
MODULE_DESCRIPTION("super-duper-nes bbb tty module.");
MODULE_VERSION("0.1");

static char *mod_name = "bbb_tty";
module_param(mod_name, charp, 0444);
MODULE_PARM_DESC(name, "module name @ /sys/module/bbb_tty_core/parameters/mod_name");

static int __init bt_module_init(void){
    int ret;

    printk(KERN_INFO "module [%s] initialize.\n", mod_name);

    ret = bt_i2c_init();
    if (ret) {
        printk(KERN_ERR "bt_i2c_init failed.\n");
        return -1;
    }

    ret = bt_gpio_init();
    if (ret) {
        printk(KERN_ERR "bt_gpio_init failed.\n");
        return -1;
    }

    ret = bbb_tty_init();
    if (ret) {
        printk(KERN_ERR "bbb_tty_init failed.\n");
        return -1;
    }

    ret = bt_proc_init();
    if (ret) {
        printk(KERN_ERR "bbb_tty_proc_init failed.\n");
        return -1;
    }

    return 0;
}

static void __exit bt_module_exit(void){
    bt_proc_exit();
    bbb_tty_exit();
    bt_i2c_exit();
    bt_gpio_exit();
    printk(KERN_INFO "module [%s] exit.\n", mod_name);
}

module_init(bt_module_init);
module_exit(bt_module_exit);
