astoria-d/super-duper-nes/duper_cartridge/simulation/testbench_duper_cartridge.vhd

library IEEE;
use IEEE.std_logic_1164.all;
use ieee.std_logic_arith.all;
use ieee.std_logic_arith.conv_std_logic_vector;


entity testbench_i2c_test is
end testbench_i2c_test;

architecture stimulus of testbench_i2c_test is 

    constant powerup_time   : time := 200 ns;
    constant reset_time     : time := 800 ns;
    constant start_time     : time := 12 us;

    --DE1 base clock = 50 MHz
    constant base_clock_time : time := 20 ns;

    --i2c normal clock speed 100 KHz
    constant i2c_clock_time : time := 10 us;

    ---https://wiki.nesdev.com/w/index.php/Clock_rate
    --nes cpu clock = 1.789773 MHz
    constant nes_clock_time : time := 558 ns;

    constant bus_cycle : integer := 3;


---fifo status register
---bit	
---7	always 0
---6	always 0
---5	read fifo full
---4	read fifo empty
---3	always 0
---2	always 0
---1	write fifo full
---0	write fifo empty
    constant wfifo_empty_bit    : integer := 0;
    constant wfifo_full_bit     : integer := 1;
    constant rfifo_empty_bit    : integer := 4;
    constant rfifo_full_bit     : integer := 5;

    constant i2c_read       : std_logic := '1';
    constant i2c_write      : std_logic := '0';

    component duper_cartridge
    port (
        pi_reset_n      : in std_logic;
        pi_base_clk     : in std_logic;

        --nes side
        pi_phi2             : in std_logic;
        pi_prg_ce_n         : in std_logic;
        pi_prg_r_nw         : in std_logic;
        pi_prg_addr         : in std_logic_vector(14 downto 0);
        pio_prg_data        : inout std_logic_vector(7 downto 0);
        pi_chr_ce_n         : in std_logic;
        pi_chr_oe_n         : in std_logic;
        pi_chr_we_n         : in std_logic;
        pi_chr_addr         : in std_logic_vector(12 downto 0);
        po_chr_data         : out std_logic_vector(7 downto 0);

        --i2c side
        pi_i2c_scl      : in    std_logic;
        pio_i2c_sda     : inout std_logic;

        --bbb gpio
        po_nes_f_full   : out   std_logic;
        po_bbb_f_empty  : out   std_logic;

        po_dbg_cnt          : out std_logic_vector (63 downto 0)
    );
    end component ;

    signal reset_input      : std_logic;
    signal base_clk         : std_logic;

    signal phi2             : std_logic;
    signal prg_ce_n         : std_logic;
    signal prg_r_nw         : std_logic;
    signal prg_addr         : std_logic_vector(14 downto 0);
    signal prg_data         : std_logic_vector(7 downto 0);
    signal chr_ce_n         : std_logic;
    signal chr_oe_n         : std_logic;
    signal chr_we_n         : std_logic;
    signal chr_addr         : std_logic_vector(12 downto 0);
    signal chr_data         : std_logic_vector(7 downto 0);

    signal i2c_scl          : std_logic;
    signal i2c_sda          : std_logic;

    signal nes_f_full       : std_logic;
    signal bbb_f_empty      : std_logic;

    signal dbg_cnt          : std_logic_vector (63 downto 0);

    signal reg_rom_data     : std_logic_vector(7 downto 0);
    signal reg_bbb_data     : std_logic_vector (7 downto 0);

    signal start_scl        : std_logic;
    signal step_cnt         : integer range 0 to 65535 := 0;
    signal stage_cnt        : integer range 0 to 65535 := 0;
    signal i2c_step_cnt     : integer range 0 to 65535 := 0;

begin

    ---chrrom side disabled..
    chr_ce_n <= 'Z';
    chr_oe_n <= 'Z';
    chr_we_n <= 'Z';
    chr_addr <= (others => 'Z');
    chr_data <= (others => 'Z');

    sim_board : duper_cartridge port map (
    reset_input,
    base_clk,

    phi2,
    prg_ce_n,
    prg_r_nw,
    prg_addr,
    prg_data,

    chr_ce_n,
    chr_oe_n,
    chr_we_n,
    chr_addr,
    chr_data,

    i2c_scl,
    i2c_sda,

    nes_f_full,
    bbb_f_empty,

    dbg_cnt);

    --- input reset.
    reset_p: process
    begin
        reset_input <= '1';
        wait for powerup_time;

        reset_input <= '0';
        wait for reset_time;

        reset_input <= '1';
        wait;
    end process;

    --- generate base clock.
    clock_p1 : process
    begin
        base_clk <= '1';
        wait for base_clock_time / 2;
        base_clk <= '0';
        wait for base_clock_time / 2;
    end process;

    --- nes clock.
    clock_p2 : process
    begin
        phi2 <= '1';
        wait for nes_clock_time / 2;
        phi2 <= '0';
        wait for nes_clock_time / 2;
    end process;

    --rom save register...
    romreg_p : process (phi2)
    begin
        if (rising_edge(phi2)) then
            --bus cycle is 1 cycle delayed.
            if (step_cnt mod bus_cycle = 1) then
                reg_rom_data <= prg_data;
            end if;
        end if;
    end process;

    --- cpu bus emulation...
    emu_cpu : process

procedure mem_write
(
    addr    : in std_logic_vector (14 downto 0);
    data    : in std_logic_vector (7 downto 0)
) is
begin
    prg_ce_n  <= '0';
    prg_r_nw  <= '0';
    prg_addr  <= addr;
    prg_data  <= data;
end;

procedure mem_read
(
    addr    : in std_logic_vector (14 downto 0)
) is
begin
    prg_ce_n  <= '0';
    prg_r_nw  <= '1';
    prg_addr  <= addr;
    prg_data  <= (others => 'Z');
end;

procedure bus_wait is
begin
    prg_ce_n  <= '1';
    prg_r_nw  <= 'Z';
    prg_addr  <= (others => 'Z');
    prg_data  <= (others => 'Z');
end;

    begin
        if (stage_cnt = 0) then
            wait for powerup_time + reset_time;
            stage_cnt <= stage_cnt + 1;
            step_cnt <= 0;
        elsif (stage_cnt = 1) then
        --pseudo rom read.
            if (step_cnt < bus_cycle * 1) then
                if (step_cnt mod bus_cycle = 0) then
                    mem_read (conv_std_logic_vector(16#fffa#, 15));
                else
                    bus_wait;
                end if;
                step_cnt <= step_cnt + 1;
            elsif (step_cnt < bus_cycle * 2) then
                if (step_cnt mod bus_cycle = 0) then
                    mem_read (conv_std_logic_vector(16#fff8#, 15));
                else
                    bus_wait;
                end if;
                step_cnt <= step_cnt + 1;
            else
                bus_wait;
                step_cnt <= 0;
                stage_cnt <= stage_cnt + 1;
            end if;
        elsif (stage_cnt = 2) then
        --polling fifo status.
            if (reg_rom_data (rfifo_empty_bit) = '1') then
                if (step_cnt mod bus_cycle = 0) then
                    mem_read (conv_std_logic_vector(16#fff8#, 15));
                else
                    bus_wait;
                end if;
                step_cnt <= step_cnt + 1;
            else
                bus_wait;
                step_cnt <= 0;
                stage_cnt <= stage_cnt + 1;
            end if;
        elsif (stage_cnt = 3) then
        --read fifo..
            --wait for test pattern.
            if (reg_rom_data /= conv_std_logic_vector(16#5a#, 8)) then
                if (step_cnt mod bus_cycle = 0) then
                    --0xfff9 is fifo read.
                    mem_read (conv_std_logic_vector(16#fff9#, 15));
                else
                    bus_wait;
                end if;
                step_cnt <= step_cnt + 1;
            else
                bus_wait;
                step_cnt <= 0;
                stage_cnt <= stage_cnt + 1;
            end if;

        elsif (stage_cnt = 4) then
        --push fifo to bbb..
            if (step_cnt mod bus_cycle = 0 and step_cnt < 30) then
                --0xfff9 is fifo write.
                mem_write (conv_std_logic_vector(16#fff9#, 15),conv_std_logic_vector(16#77# + step_cnt, 8));
                step_cnt <= step_cnt + 1;
            elsif (step_cnt mod bus_cycle = 0 and step_cnt = 30) then
                bus_wait;
                step_cnt <= 0;
                stage_cnt <= stage_cnt + 1;
            else
                bus_wait;
                step_cnt <= step_cnt + 1;
            end if;

        elsif (stage_cnt = 5) then
        --polling fifo status.
            if (step_cnt = 0) then
                mem_read (conv_std_logic_vector(16#fff8#, 15));
                step_cnt <= step_cnt + 1;
            else
                if (reg_rom_data (wfifo_empty_bit) = '0') then
                    if (step_cnt mod bus_cycle = 0) then
                        mem_read (conv_std_logic_vector(16#fff8#, 15));
                    else
                        bus_wait;
                    end if;
                    step_cnt <= step_cnt + 1;
                else
                    bus_wait;
                    step_cnt <= 0;
                    stage_cnt <= stage_cnt + 1;
                end if;
            end if;

        else
            bus_wait;
            stage_cnt <= stage_cnt + 1;
        end if;
        wait for nes_clock_time;
    end process;


    --- i2c_scl process..
    scl_p : process
    begin
        if(start_scl = '1') then
            i2c_scl <= '1';
            wait for i2c_clock_time / 2;
            i2c_scl <= '0';
            wait for i2c_clock_time / 2;
        else
            i2c_scl <= '1';
            wait for i2c_clock_time;
        end if;
    end process;

    i2c_cnt_p : process
    begin
        if (stage_cnt = 2) then
            i2c_step_cnt <= i2c_step_cnt + 1;
        elsif (stage_cnt = 3) then
            if (i2c_step_cnt = 22) then
                i2c_step_cnt <= 0;
            else
                i2c_step_cnt <= i2c_step_cnt + 1;
            end if;
        elsif (stage_cnt = 5) then
            i2c_step_cnt <= i2c_step_cnt + 1;
        else
            i2c_step_cnt <= 0;
        end if;
        wait for i2c_clock_time;
    end process;



    --- i2c_scl process..
    i2c_scl_handl_p : process
    begin
        if (stage_cnt = 0) then
            start_scl <= '0';
        elsif (stage_cnt = 2) then
            start_scl <= '1';
        elsif (stage_cnt = 3) then
            if (step_cnt < 50) then
                start_scl <= '0';
            else
                start_scl <= '1';
            end if;
        elsif (stage_cnt = 5) then
            if (step_cnt < 50) then
                start_scl <= '0';
            else
                start_scl <= '1';
            end if;
        else
            start_scl <= '0';
        end if;
        wait for nes_clock_time;
    end process;



    --- i2c_sda process..
    i2c_p : process

variable remaining_time : time;
variable start_index : integer;


procedure wait_clock
(
    wait_time : in time
) is
begin
    wait for wait_time;
    remaining_time := remaining_time - wait_time;
end;

procedure wait_remaining is
begin
    wait for remaining_time;
end;

procedure output_addr
(
    i       : in integer;
    addr    : in std_logic_vector (6 downto 0)
) is
begin
    i2c_sda <= addr(i);
end;

procedure ack_wait is
begin
    i2c_sda <= 'Z';
end;

procedure output_data
(
    i       : in integer;
    data    : in std_logic_vector (7 downto 0)
) is
begin
    i2c_sda <= data(i);
end;

procedure input_data
(
    i       : in integer
) is
begin
    reg_bbb_data(i) <= i2c_sda;
end;


    begin
        remaining_time := i2c_clock_time;
        if (stage_cnt = 2) then
        --from bbb to nes i2c write.
            if (i2c_step_cnt = 0) then
                start_index := 0;
            elsif (i2c_step_cnt = 1) then
                --start up seq...
                wait_clock (i2c_clock_time / 4);
                i2c_sda <= '0';

                --set i2c addr...
                --addr output with write.....
                --0x44 = 100 0101.
                start_index := i2c_step_cnt;
                wait_clock (i2c_clock_time / 2);
                output_addr(6 - i2c_step_cnt + start_index, conv_std_logic_vector(16#44#, 7));

            elsif (i2c_step_cnt <= 7) then
                wait_clock (i2c_clock_time * 3 / 4);
                output_addr(6 - i2c_step_cnt + start_index, conv_std_logic_vector(16#44#, 7));

            elsif (i2c_step_cnt = 8) then
                wait_clock (i2c_clock_time * 3 / 4);
                i2c_sda <= i2c_write;

            elsif (i2c_step_cnt = 9) then
                --wait ack...
                wait_clock (i2c_clock_time * 3 / 4);
                ack_wait;

            --output data
            elsif (i2c_step_cnt = 10) then
                start_index := i2c_step_cnt;
                wait_clock (i2c_clock_time * 3 / 4);
                output_data(8 - i2c_step_cnt + start_index, conv_std_logic_vector(16#55#, 8));

            elsif (i2c_step_cnt <= 17) then
                wait_clock (i2c_clock_time * 3 / 4);
                output_data(8 - i2c_step_cnt + start_index, conv_std_logic_vector(16#55#, 8));

            elsif (i2c_step_cnt = 18) then
                --wait ack...
                wait_clock (i2c_clock_time * 3 / 4);
                ack_wait;

            elsif (i2c_step_cnt = 20) then
                --stop seq...
                i2c_sda <= '0';
                wait_clock (i2c_clock_time / 4);
                i2c_sda <= '1';
            end if;

        elsif (stage_cnt = 3) then
        --from bbb to nes i2c write.
            if (i2c_step_cnt = 0) then
                start_index := 0;
            elsif (i2c_step_cnt = 1) then
                --start up seq...
                wait_clock (i2c_clock_time / 4);
                i2c_sda <= '0';

                --set i2c addr...
                --addr output with write.....
                --0x44 = 100 0101.
                start_index := i2c_step_cnt;
                wait_clock (i2c_clock_time / 2);
                output_addr(6 - i2c_step_cnt + start_index, conv_std_logic_vector(16#44#, 7));

            elsif (i2c_step_cnt <= 7) then
                wait_clock (i2c_clock_time * 3 / 4);
                output_addr(6 - i2c_step_cnt + start_index, conv_std_logic_vector(16#44#, 7));

            elsif (i2c_step_cnt = 8) then
                wait_clock (i2c_clock_time * 3 / 4);
                i2c_sda <= i2c_write;

            elsif (i2c_step_cnt = 9) then
                --wait ack...
                wait_clock (i2c_clock_time * 3 / 4);
                ack_wait;

            --output data
            elsif (i2c_step_cnt = 10) then
                start_index := i2c_step_cnt;
                wait_clock (i2c_clock_time * 3 / 4);
                output_data(8 - i2c_step_cnt + start_index, conv_std_logic_vector(16#5a#, 8));

            elsif (i2c_step_cnt <= 17) then
                wait_clock (i2c_clock_time * 3 / 4);
                output_data(8 - i2c_step_cnt + start_index, conv_std_logic_vector(16#5a#, 8));

            elsif (i2c_step_cnt = 18) then
                --wait ack...
                wait_clock (i2c_clock_time * 3 / 4);
                ack_wait;

            elsif (i2c_step_cnt = 20) then
                --stop seq...
                i2c_sda <= '0';
                wait_clock (i2c_clock_time / 4);
                i2c_sda <= '1';
            end if;

        elsif (stage_cnt = 5) then
        --from bbb to nes i2c read.
            if (i2c_step_cnt <= 3) then
                start_index := i2c_step_cnt;
            elsif (i2c_step_cnt = 4) then
                --start up seq...
                wait_clock (i2c_clock_time / 4);
                i2c_sda <= '0';

                --set i2c addr...
                --addr output with write.....
                --0x44 = 100 0101.
                start_index := i2c_step_cnt;
                wait_clock (i2c_clock_time / 2);
                output_addr(6 - i2c_step_cnt + start_index, conv_std_logic_vector(16#44#, 7));

            elsif (i2c_step_cnt <= 10) then
                wait_clock (i2c_clock_time * 3 / 4);
                output_addr(6 - i2c_step_cnt + start_index, conv_std_logic_vector(16#44#, 7));

            elsif (i2c_step_cnt = 11) then
                wait_clock (i2c_clock_time * 3 / 4);
                i2c_sda <= i2c_read;

            elsif (i2c_step_cnt = 12) then
                --wait ack...
                wait_clock (i2c_clock_time * 3 / 4);
                start_index := i2c_step_cnt + 1;
                ack_wait;

            --read data
            elsif (i2c_step_cnt >= 14 and i2c_step_cnt <= 21) then
                input_data(7 - i2c_step_cnt + start_index);

            elsif (i2c_step_cnt = 22) then
                --return ack...
                wait_clock (i2c_clock_time * 3 / 4);
                i2c_sda <= '0';

            elsif (i2c_step_cnt = 23) then
                --stop seq...
                i2c_sda <= '0';
                wait_clock (i2c_clock_time / 4);
                i2c_sda <= '1';
            end if;

        else
            --pull up.
            i2c_sda <= '1';
        end if;
        wait_remaining;
    end process;

end stimulus;
